bowseruk/voron-2-300/stl/Electronics Bay/Wago_3x_221-415_DIN_Mount.stl

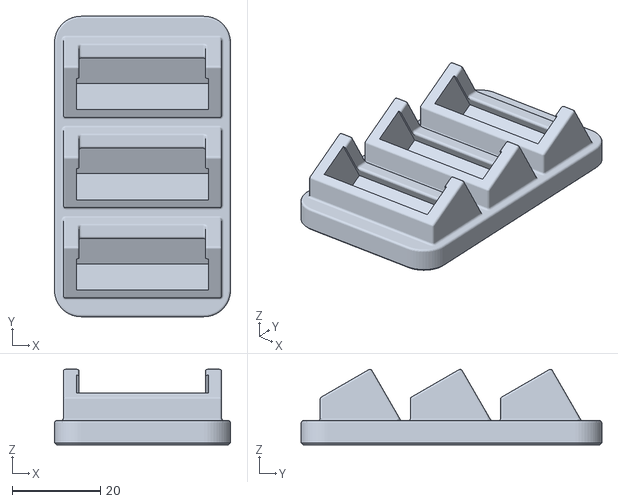
[picture p15: CAD file, 2023-08-16]
stl/Electronics Bay/Wago_3x_221-415_DIN_Mount.stl
40.0 x 68.3 x 17.2
