bowseruk/voron-2-300/stl/Exhaust FIlter/exhaust_filter_housing(r2)Filament-Sensor.stl

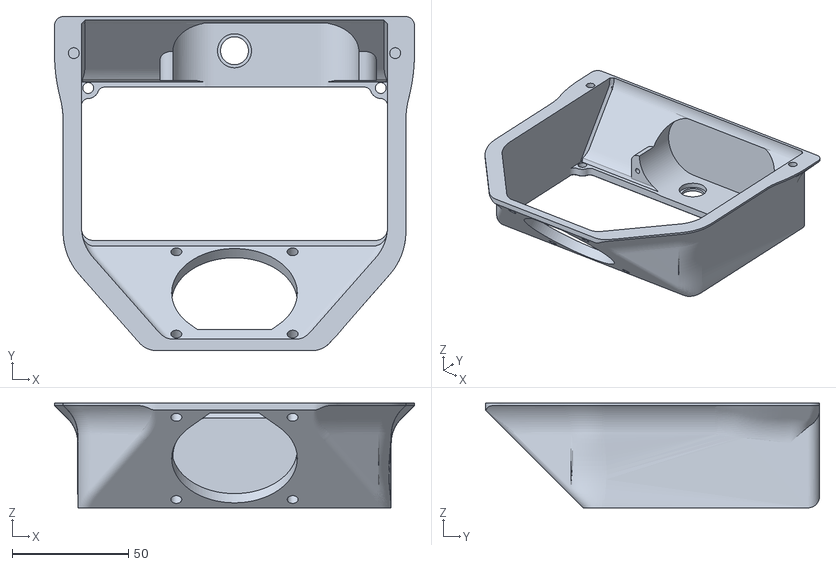
[picture p16: CAD file, 2024-02-13]
stl/Exhaust FIlter/exhaust_filter_housing(r2)Filament-Sensor.stl
154.8 x 143.7 x 45.0
