bowseruk/voron-2-300/stl/Gantry/z_joint_igus_kglm-05_x4.stl

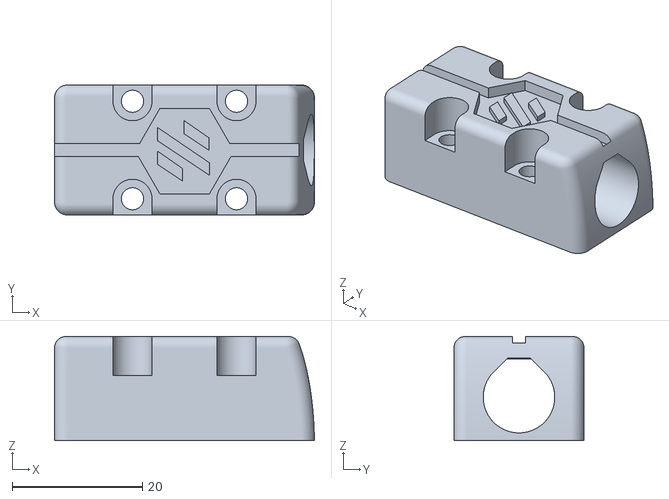
[picture p17: CAD file, 2023-08-16]
stl/Gantry/z_joint_igus_kglm-05_x4.stl
40.0 x 20.0 x 16.0
