bowseruk/voron-2-300/stl/Panel Mount/magnetic_door_hinge_tape_v2__5mm.stl

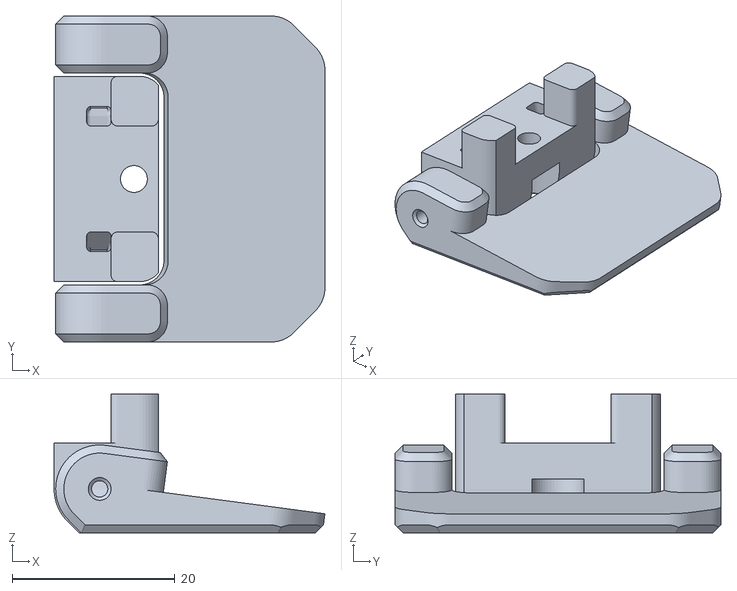
[picture p18: CAD file, 2023-12-29]
stl/Panel Mount/magnetic_door_hinge_tape_v2__5mm.stl
33.2 x 40.0 x 17.0
