bowseruk/voron-2-300/stl/Skirts/[a]_belt_guard_b_x2.stl

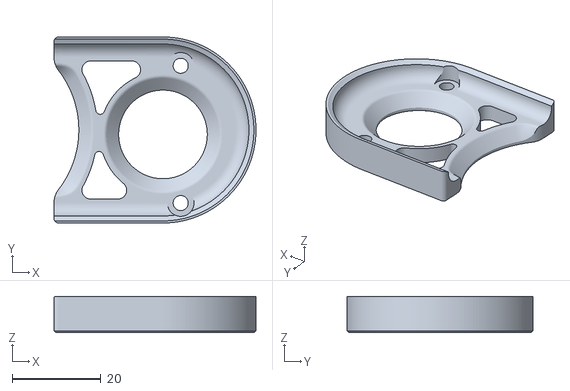
[picture p19: CAD file, 2023-08-16]
stl/Skirts/[a]_belt_guard_b_x2.stl
45.6 x 42.0 x 8.20
