bowseruk/voron-2-300/stl/Spool Management/bowden_retainer.stl

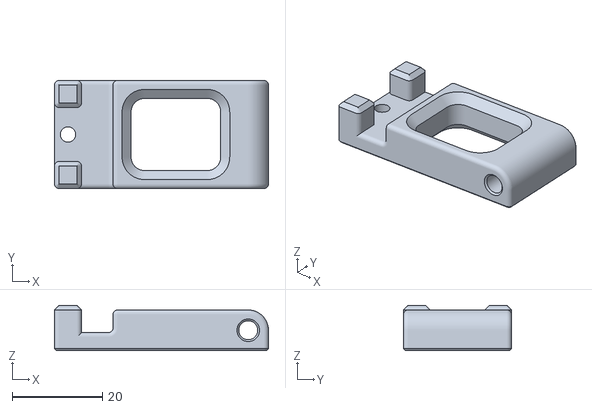
[picture p20: CAD file, 2023-08-16]
stl/Spool Management/bowden_retainer.stl
47.5 x 24.0 x 10.00
