bowseruk/voron-2-300/stl/Stealthburner/cable_door_for_pcb.stl

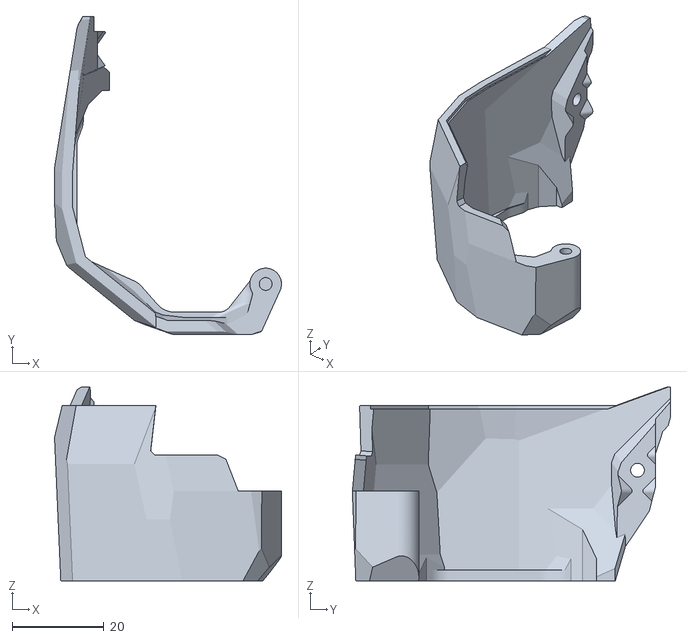
[picture p21: CAD file, 2023-08-16]
stl/Stealthburner/cable_door_for_pcb.stl
49.5 x 69.4 x 42.2
