bowseruk/voron-2-300/stl/Tools/MGN9_rail_guide_x2.stl

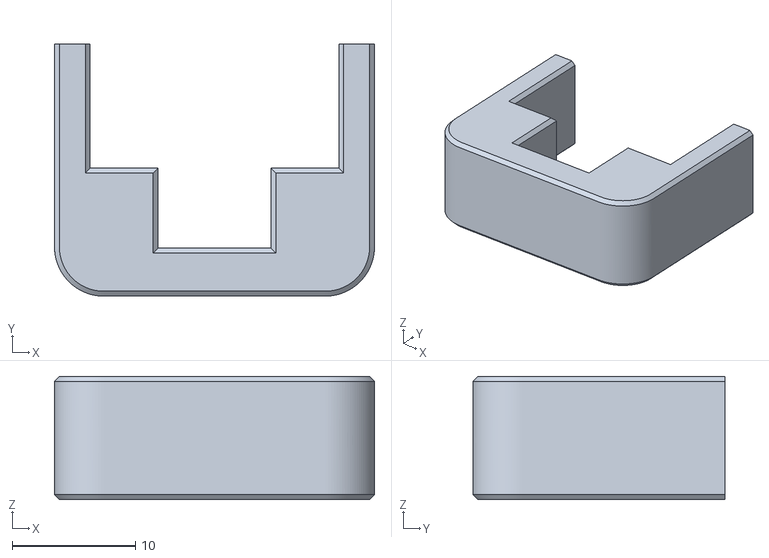
[picture p22: CAD file, 2023-08-16]
stl/Tools/MGN9_rail_guide_x2.stl
26.0 x 20.5 x 10.0
