bowseruk/voron-2-300/stl/Bed/Bed_WAGO.stl

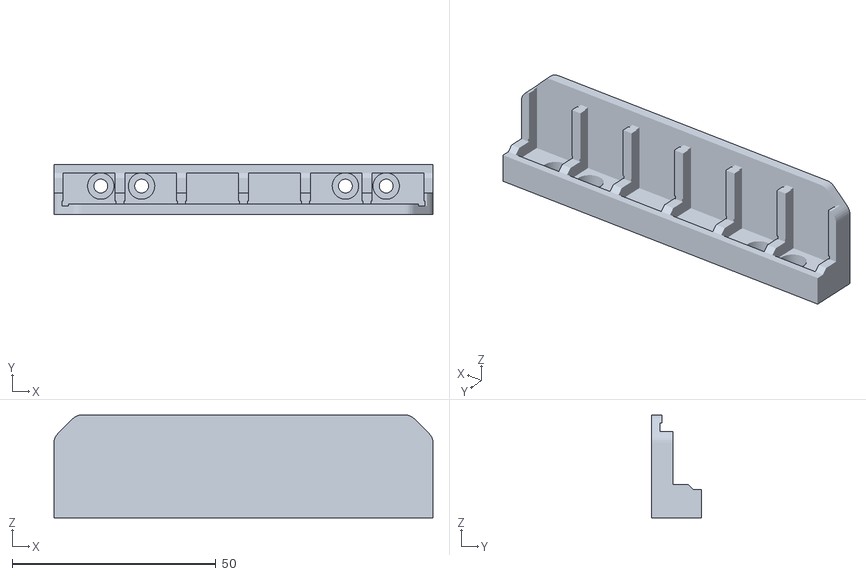
[picture p23: CAD file, 2023-08-16]
stl/Bed/Bed_WAGO.stl
92.9 x 12.2 x 25.3
