bowseruk/voron-2-300/stl/Electronics Bay/BTT_UPS_24V_DIN.stl

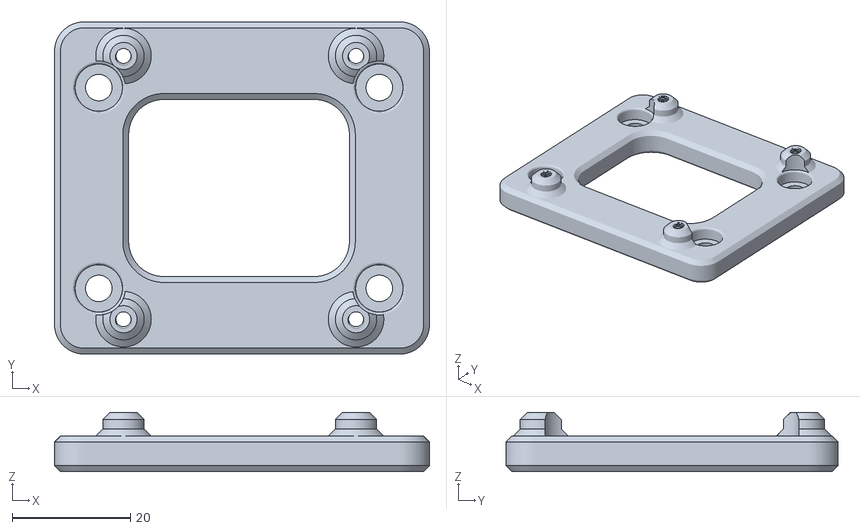
[picture p24: CAD file, 2023-08-16]
stl/Electronics Bay/BTT_UPS_24V_DIN.stl
63.5 x 56.2 x 10.0
