bowseruk/voron-2-300/stl/Exhaust FIlter/1_coal_with_mesh.stl

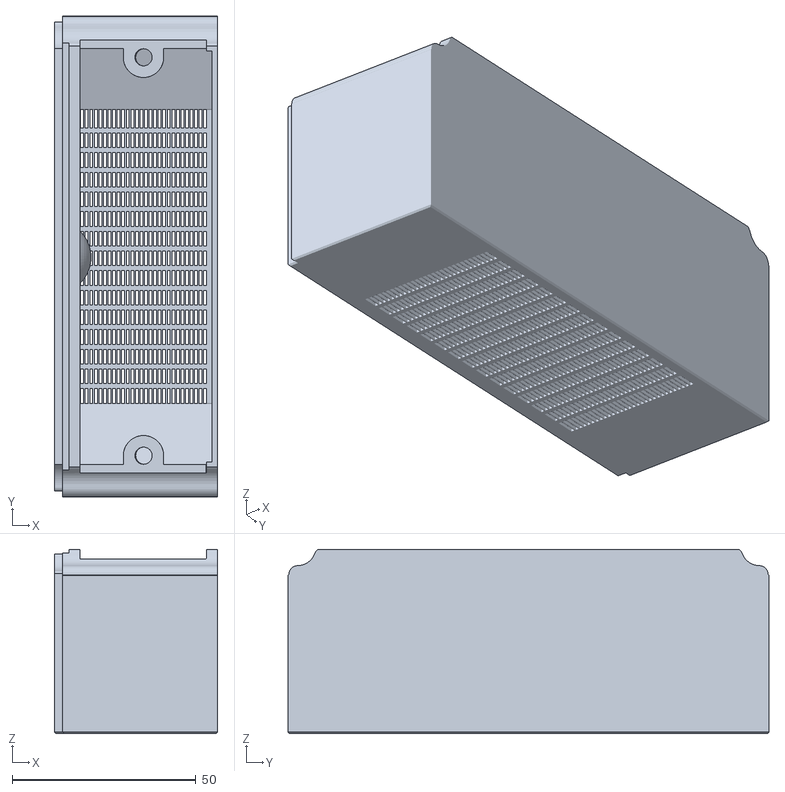
[picture p25: CAD file, 2024-02-13]
stl/Exhaust FIlter/1_coal_with_mesh.stl
44.5 x 131.0 x 50.2
