bowseruk/voron-2-300/stl/Frame/Short_Arm.stl

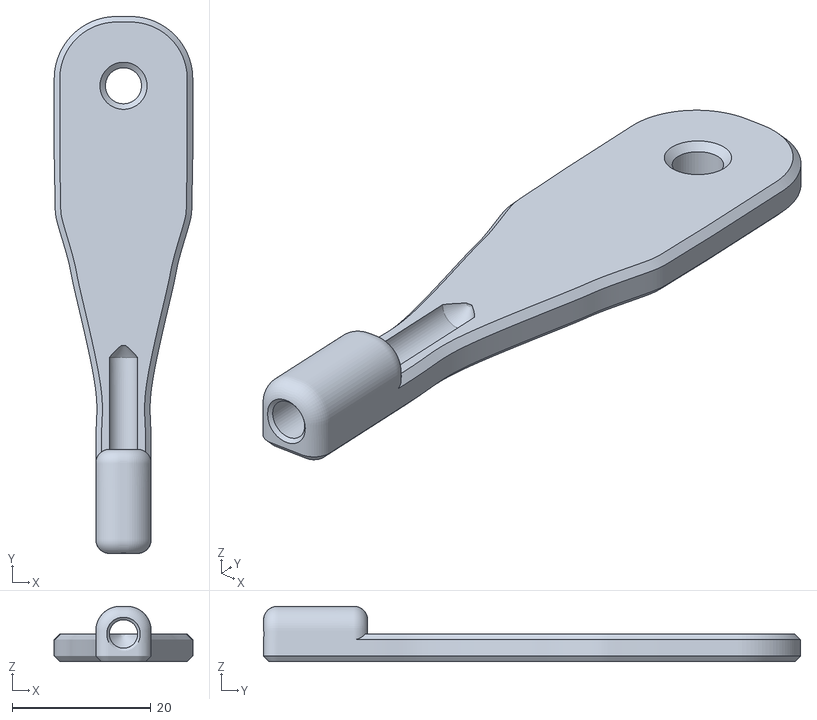
[picture p26: CAD file, 2023-08-30]
stl/Frame/Short_Arm.stl
20.0 x 77.5 x 8.00
