bowseruk/voron-2-300/stl/Gantry/z_joint_ge5c_igus_eglm-05_hall_effect_x1.stl

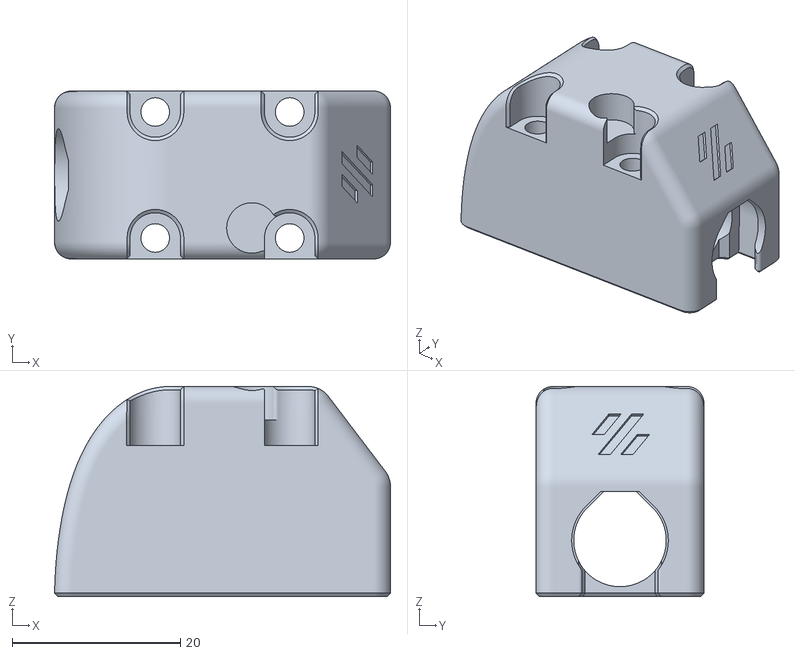
[picture p27: CAD file, 2023-08-16]
stl/Gantry/z_joint_ge5c_igus_eglm-05_hall_effect_x1.stl
40.0 x 20.0 x 25.0
