bowseruk/voron-2-300/stl/Panel Mount/Corner-Clip-7mm.stl

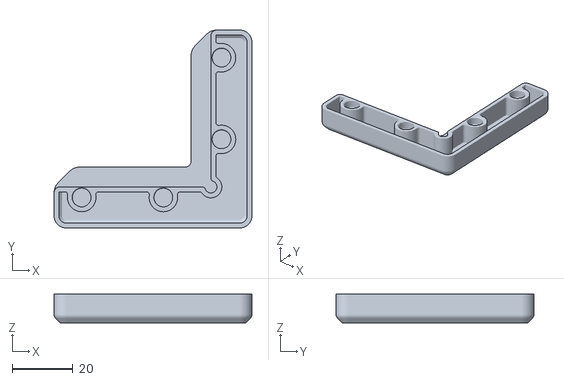
[picture p28: CAD file, 2023-12-29]
stl/Panel Mount/Corner-Clip-7mm.stl
65.0 x 65.0 x 9.50
