bowseruk/voron-2-300/stl/Skirts/front_skirt_b_300.stl

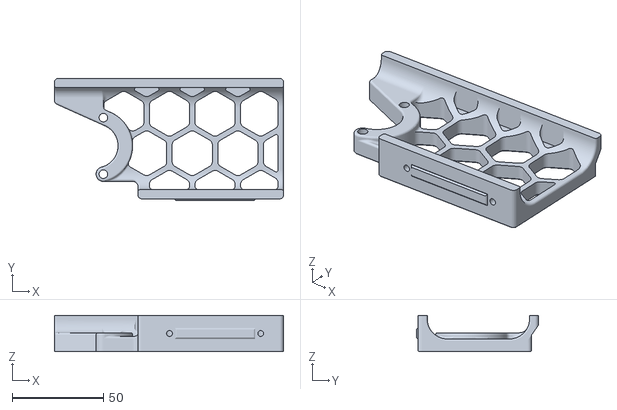
[picture p29: CAD file, 2023-08-16]
stl/Skirts/front_skirt_b_300.stl
125.5 x 67.0 x 20.0
