bowseruk/voron-2-300/stl/Stealthburner/stealthburner_printhead_dragon_rear_cw2.stl

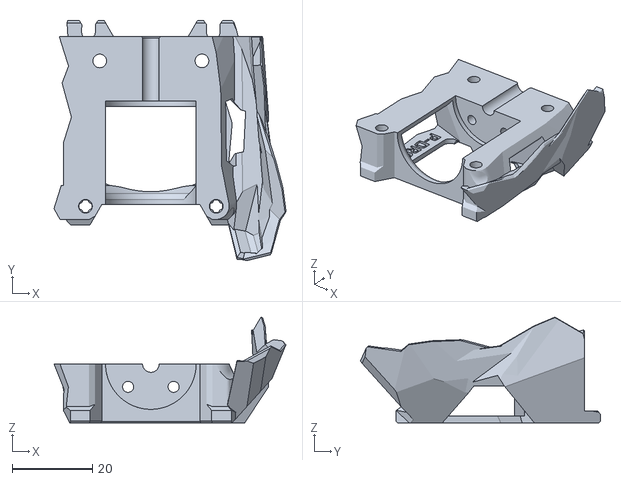
[picture p30: CAD file, 2023-08-16]
stl/Stealthburner/stealthburner_printhead_dragon_rear_cw2.stl
57.7 x 59.7 x 26.3
