bowseruk/voron-2-300/stl/Tools/pulley_jig.stl

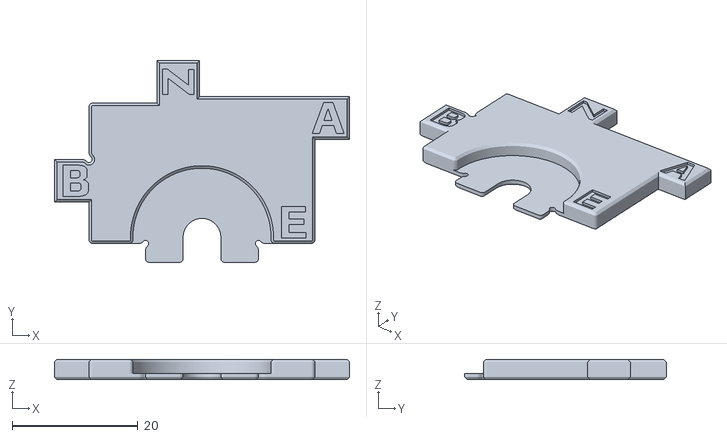
[picture p31: CAD file, 2023-08-16]
stl/Tools/pulley_jig.stl
47.0 x 32.2 x 3.20
