bowseruk/voron-2-300/stl/Z Drive/[a]_z_drive_baseplate_a_x2.stl

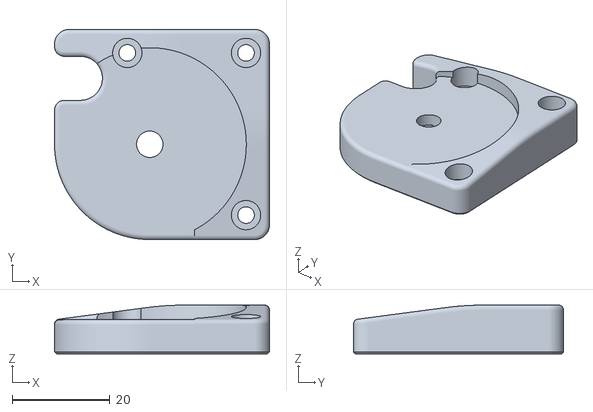
[picture p32: CAD file, 2023-08-16]
stl/Z Drive/[a]_z_drive_baseplate_a_x2.stl
44.0 x 43.0 x 10.0
