bowseruk/voron-2-300/stl/Bed/V2_Duo_Plenum.stl

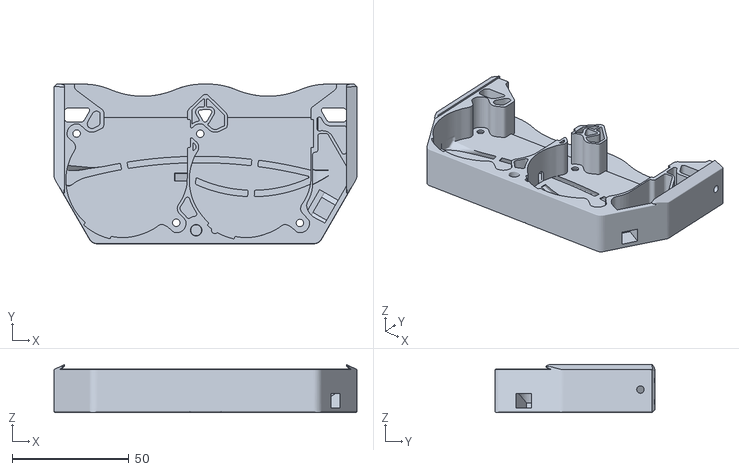
[picture p33: CAD file, 2023-08-16]
stl/Bed/V2_Duo_Plenum.stl
130.0 x 68.6 x 20.6
