bowseruk/voron-2-300/stl/Electronics Bay/RPI_Metal_DIN_Mount.stl

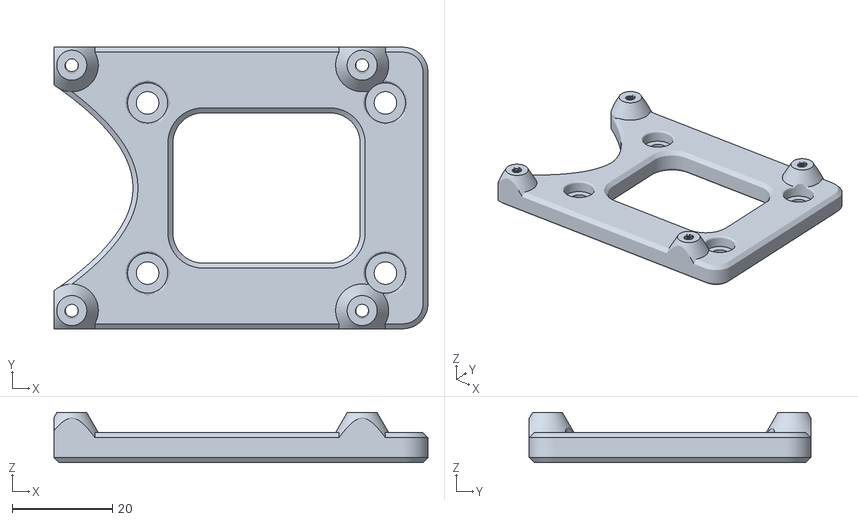
[picture p34: CAD file, 2023-08-16]
stl/Electronics Bay/RPI_Metal_DIN_Mount.stl
74.7 x 56.2 x 10.0
