bowseruk/voron-2-300/stl/Exhaust FIlter/1_hepa.stl

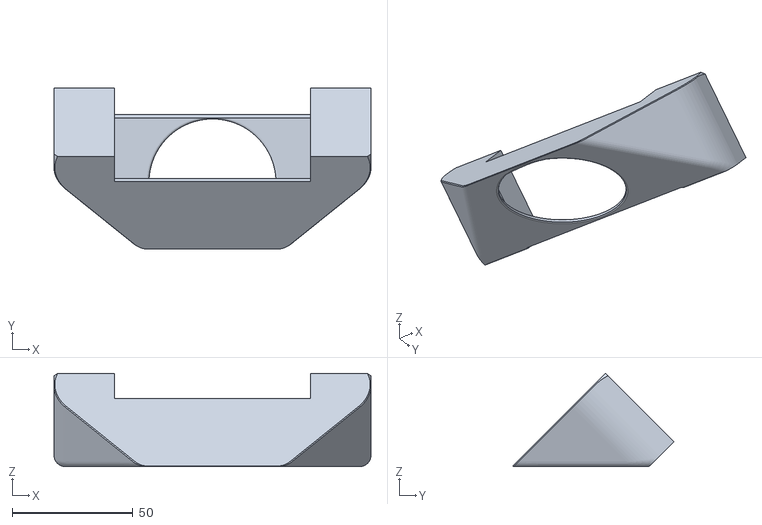
[picture p35: CAD file, 2024-02-13]
stl/Exhaust FIlter/1_hepa.stl
131.1 x 66.6 x 38.5
