bowseruk/voron-2-300/stl/Frame/arm_mount_over_led.stl

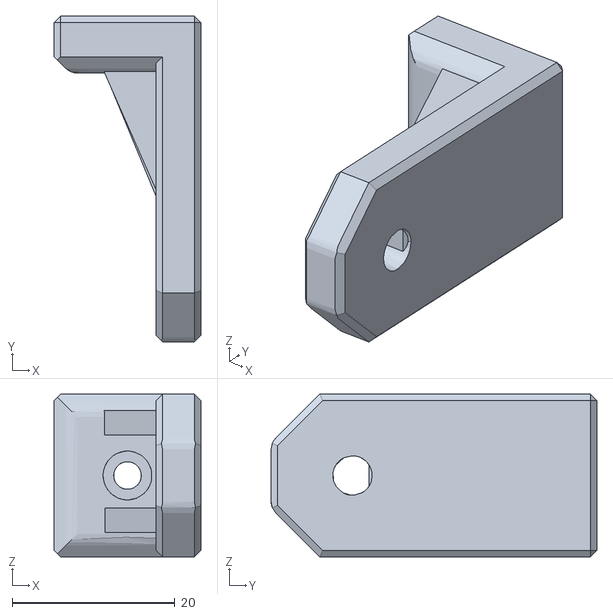
[picture p36: CAD file, 2023-08-30]
stl/Frame/arm_mount_over_led.stl
18.0 x 40.0 x 20.0
