bowseruk/voron-2-300/stl/Gantry/Z_Chain_Guide_Thermistor_Mount.stl

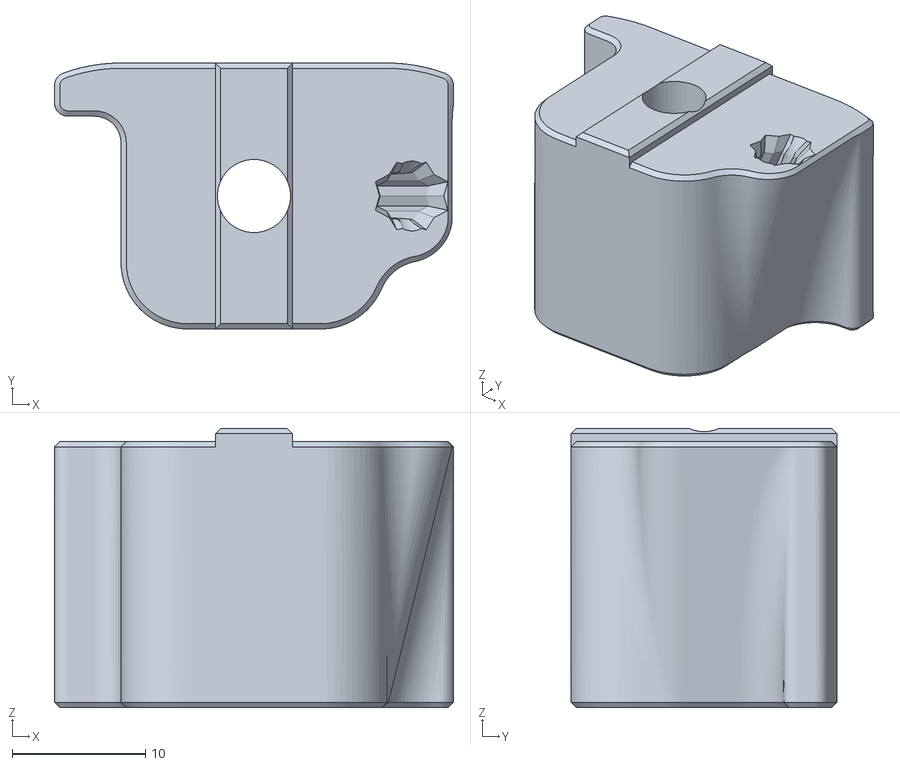
[picture p37: CAD file, 2023-08-16]
stl/Gantry/Z_Chain_Guide_Thermistor_Mount.stl
30.0 x 20.0 x 21.0
