bowseruk/voron-2-300/stl/Panel Mount/Corner-Clip-6mm.stl

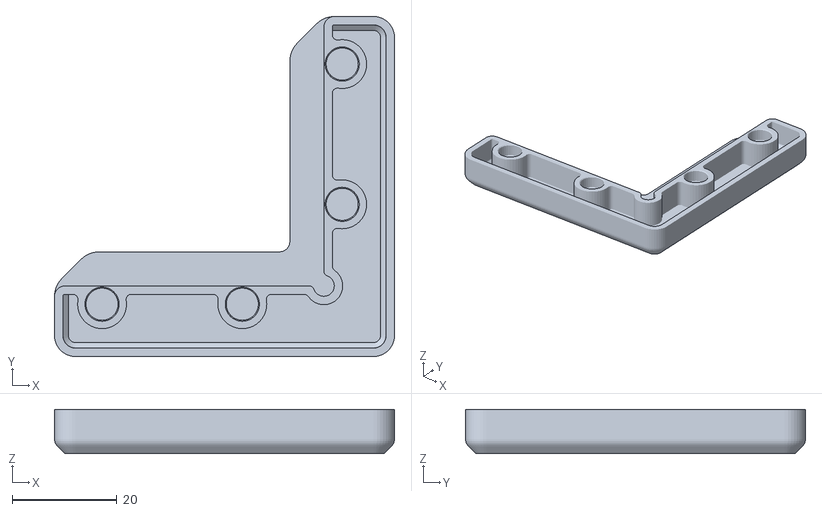
[picture p38: CAD file, 2023-12-29]
stl/Panel Mount/Corner-Clip-6mm.stl
65.0 x 65.0 x 8.50
