bowseruk/voron-2-300/stl/Skirts/[a]_keystone_blank_insert.stl

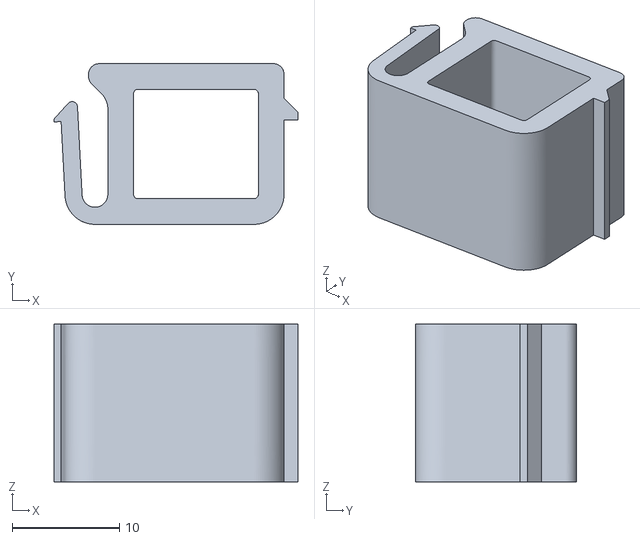
[picture p39: CAD file, 2023-08-16]
stl/Skirts/[a]_keystone_blank_insert.stl
22.8 x 15.0 x 14.7
