bowseruk/voron-2-300/stl/Stealthburner/[o]_stealthburner_LED_carrier.stl

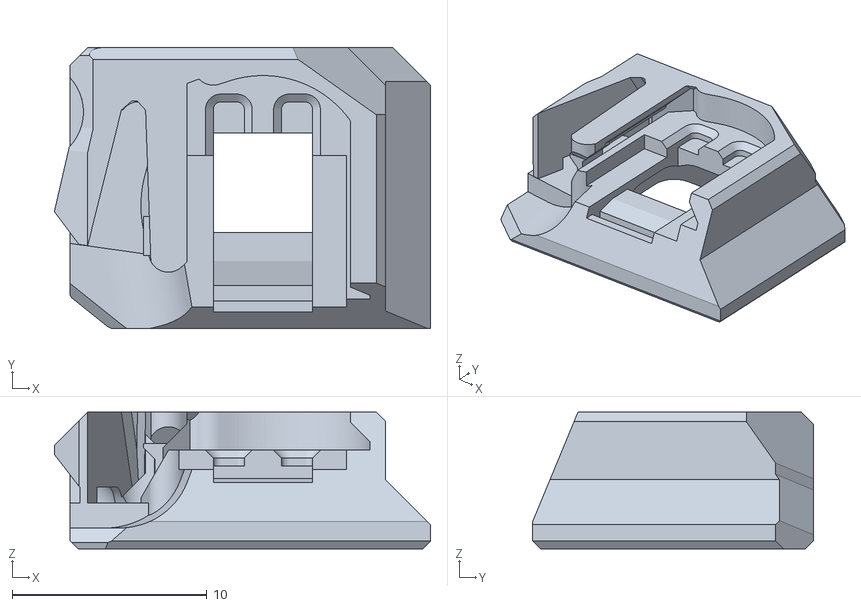
[picture p40: CAD file, 2023-08-16]
stl/Stealthburner/[o]_stealthburner_LED_carrier.stl
19.3 x 14.4 x 7.01
