bowseruk/voron-2-300/stl/Tools/MGN12_rail_guide_x2.stl

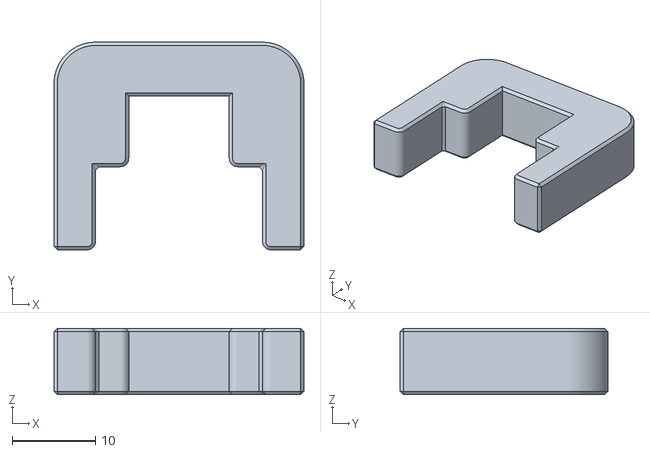
[picture p41: CAD file, 2023-08-16]
stl/Tools/MGN12_rail_guide_x2.stl
30.1 x 25.0 x 8.00
