bowseruk/voron-2-300/stl/Z Drive/z_motor_mount_b_x2.stl

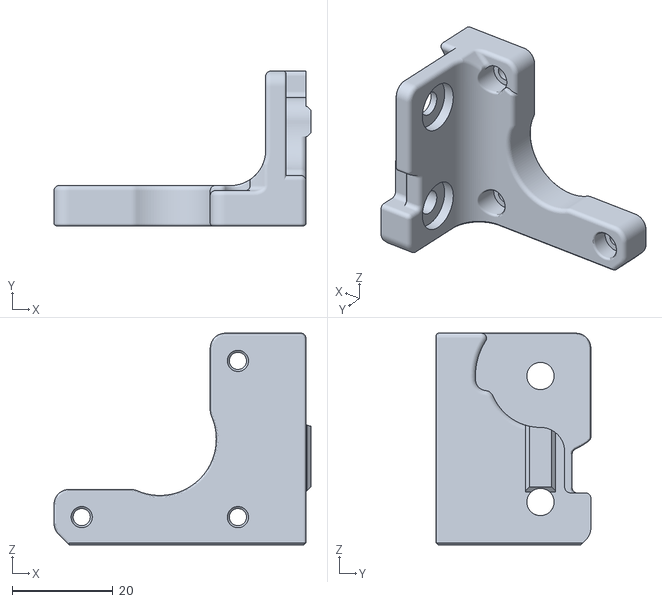
[picture p42: CAD file, 2023-08-16]
stl/Z Drive/z_motor_mount_b_x2.stl
51.0 x 30.7 x 42.0
