bowseruk/voron-2-300/stl/Bed/V2_Duo_Plenum_LID.stl

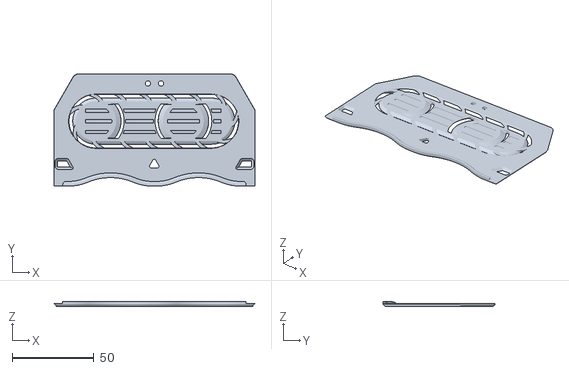
[picture p43: CAD file, 2023-08-16]
stl/Bed/V2_Duo_Plenum_LID.stl
122.8 x 68.5 x 2.80
