bowseruk/voron-2-300/stl/Electronics Bay/wago_221-415_mount_3by5.stl

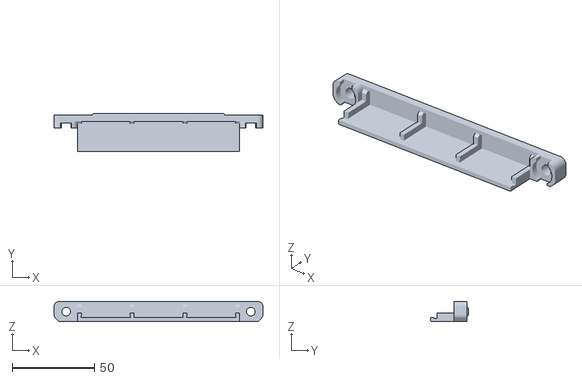
[picture p44: CAD file, 2023-08-16]
stl/Electronics Bay/wago_221-415_mount_3by5.stl
126.8 x 23.0 x 12.2
