bowseruk/voron-2-300/stl/Exhaust FIlter/exhaust_filter_housing.stl

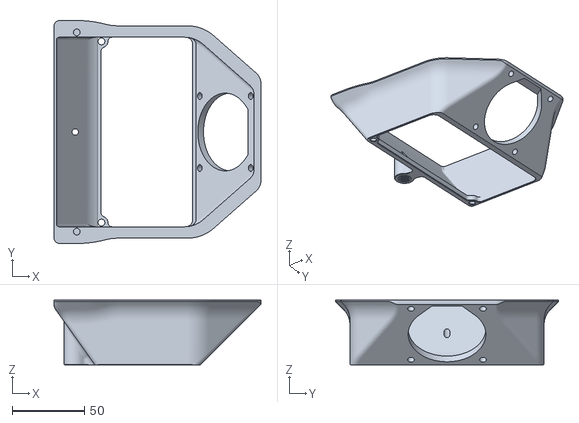
[picture p45: CAD file, 2023-08-16]
stl/Exhaust FIlter/exhaust_filter_housing.stl
143.7 x 154.8 x 45.0
