bowseruk/voron-2-300/stl/Frame/[a]_handle_middle_part.stl

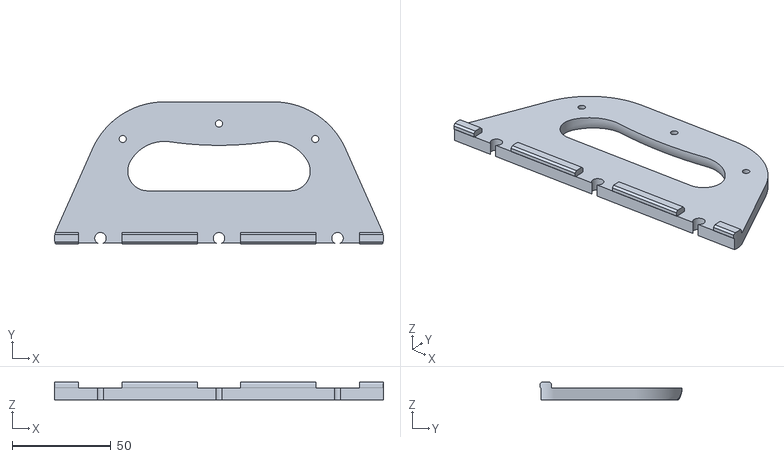
[picture p46: CAD file, 2023-08-21]
stl/Frame/[a]_handle_middle_part.stl
166.5 x 72.0 x 9.00
