bowseruk/voron-2-300/stl/Gantry/[a]_z_belt_clip_upper_x4.stl

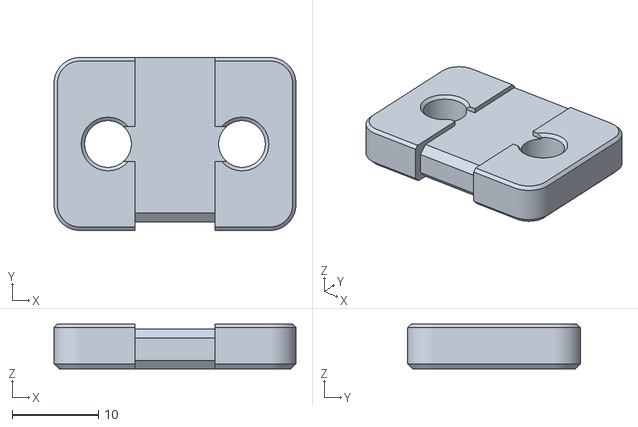
[picture p47: CAD file, 2023-08-16]
stl/Gantry/[a]_z_belt_clip_upper_x4.stl
28.0 x 20.0 x 5.20
