bowseruk/voron-2-300/stl/Panel Mount/Midspan-Clip-4mm.stl

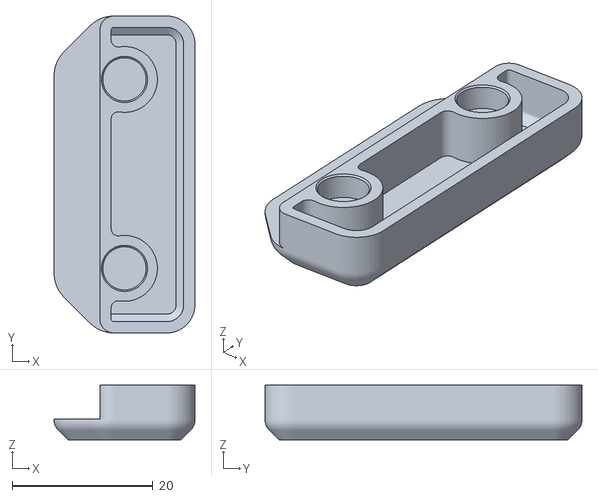
[picture p48: CAD file, 2023-12-29]
stl/Panel Mount/Midspan-Clip-4mm.stl
20.0 x 45.0 x 7.80
