bowseruk/voron-2-300/stl/Skirts/side_fan_support_x2.stl

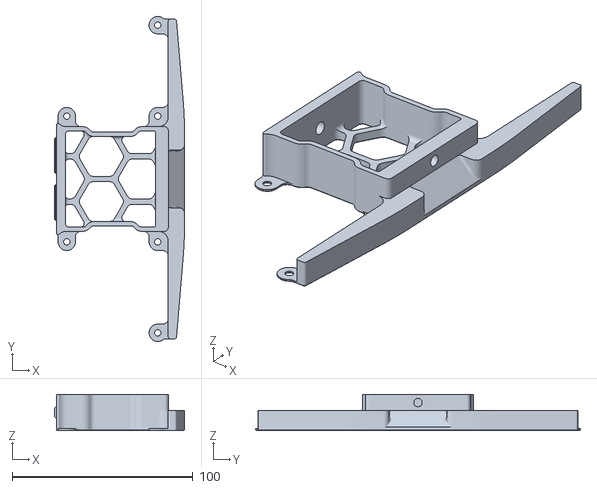
[picture p49: CAD file, 2023-08-16]
stl/Skirts/side_fan_support_x2.stl
72.0 x 180.0 x 20.0
