bowseruk/voron-2-300/stl/Stealthburner/[c]_stealthburner_LED_diffuser.stl

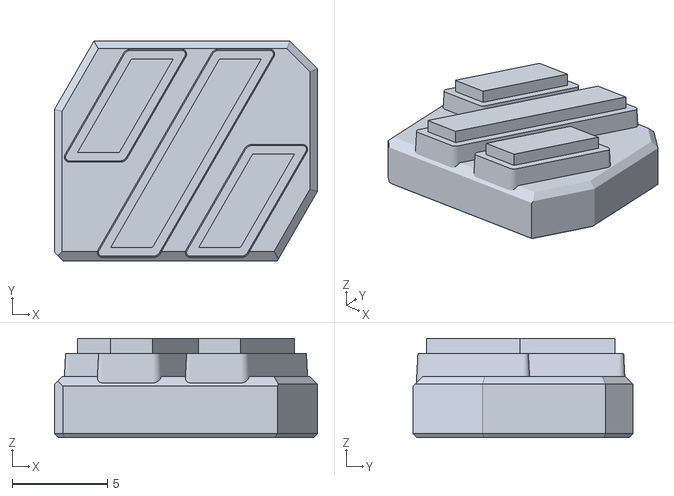
[picture p50: CAD file, 2023-08-16]
stl/Stealthburner/[c]_stealthburner_LED_diffuser.stl
13.8 x 11.5 x 5.20
