bowseruk/voron-2-300/stl/Tools/[a]_guidler_b.stl

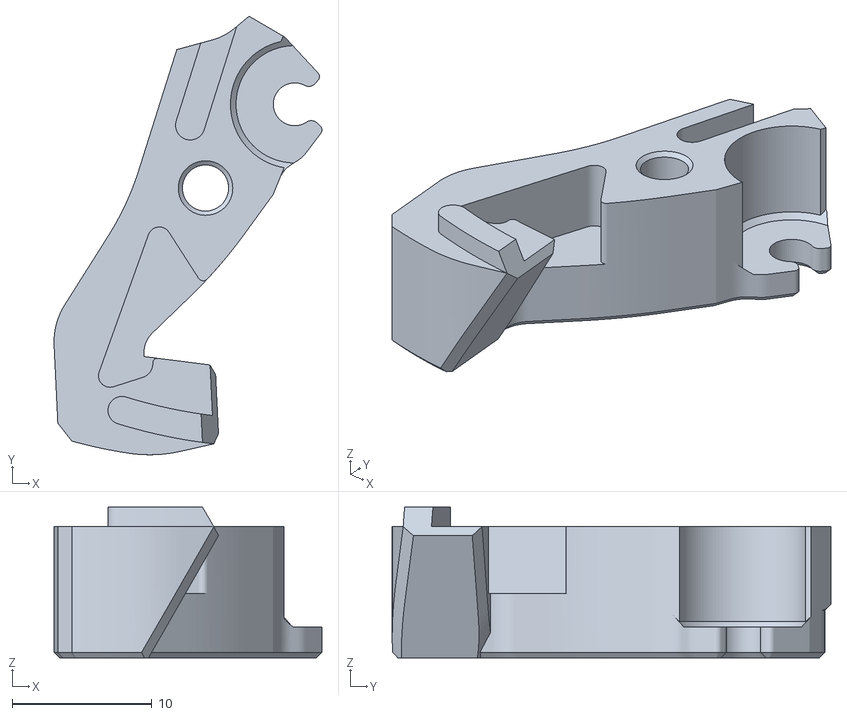
[picture p51: CAD file, 2023-08-16]
stl/Tools/[a]_guidler_b.stl
19.2 x 31.4 x 10.8
