bowseruk/voron-2-300/stl/Electronics Bay/pcb_din_clip_x3.stl

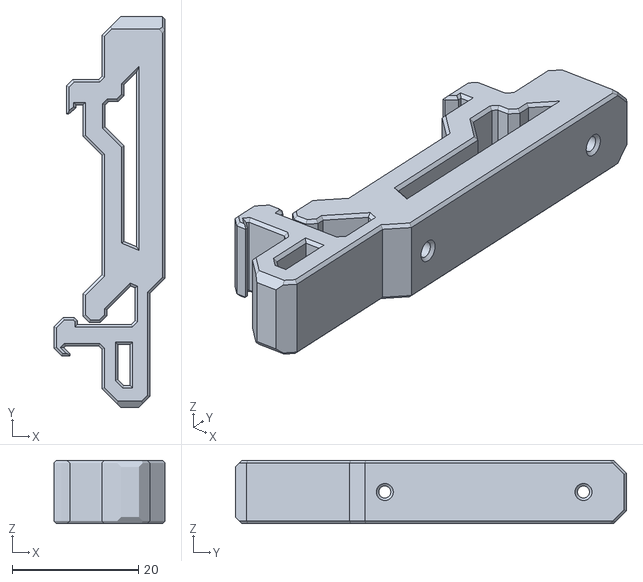
[picture p52: CAD file, 2023-08-16]
stl/Electronics Bay/pcb_din_clip_x3.stl
17.6 x 62.0 x 10.0
