bowseruk/voron-2-300/stl/Exhaust FIlter/exhaust_filter_grill.stl

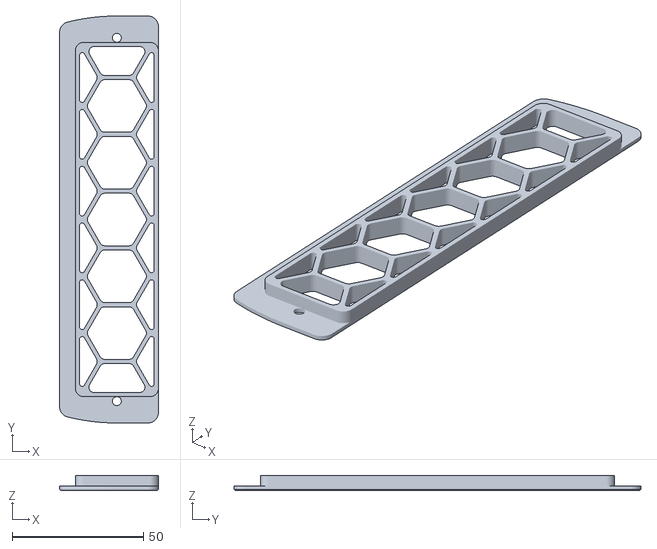
[picture p53: CAD file, 2023-08-16]
stl/Exhaust FIlter/exhaust_filter_grill.stl
37.6 x 154.8 x 5.60
