bowseruk/voron-2-300/stl/Frame/LED Spacer.stl

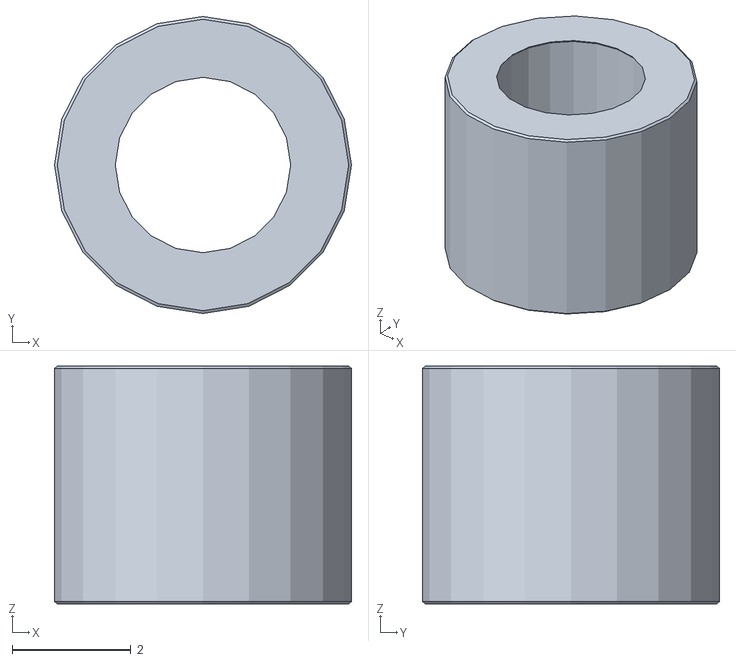
[picture p54: CAD file, 2023-08-20]
stl/Frame/LED Spacer.stl
5.00 x 5.00 x 4.00
