bowseruk/voron-2-300/stl/Gantry/[a]_z_chain_retainer_bracket_x2.stl

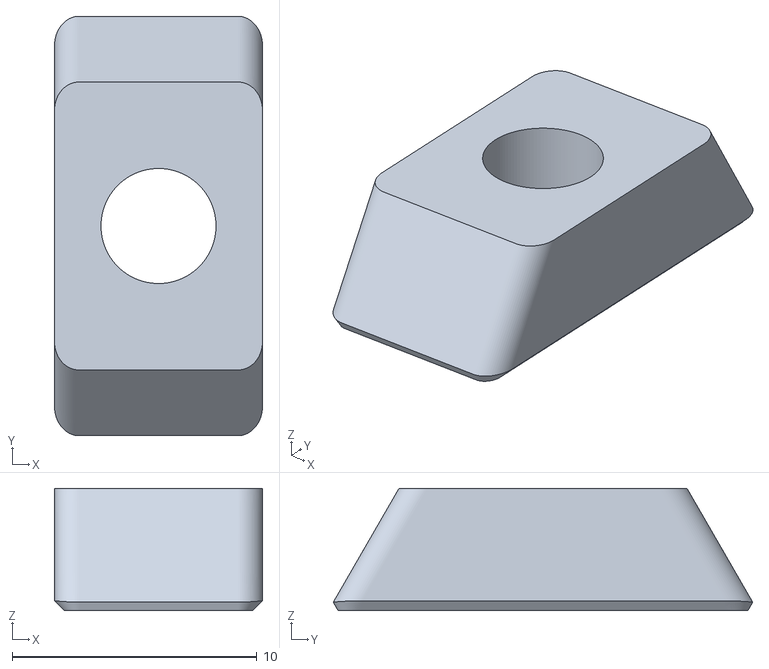
[picture p55: CAD file, 2023-08-16]
stl/Gantry/[a]_z_chain_retainer_bracket_x2.stl
8.50 x 17.1 x 5.00
