bowseruk/voron-2-300/stl/Panel Mount/Midspan-Clip-6mm.stl

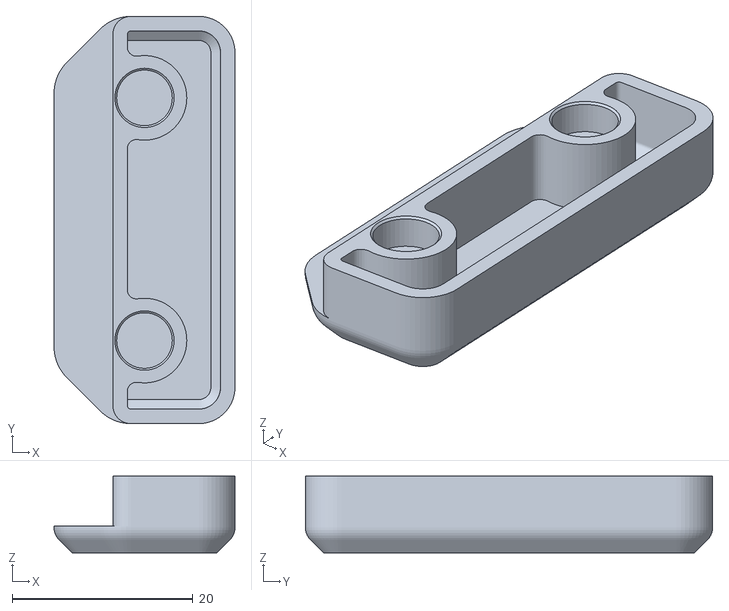
[picture p56: CAD file, 2023-12-29]
stl/Panel Mount/Midspan-Clip-6mm.stl
20.0 x 45.0 x 8.50
