bowseruk/voron-2-300/stl/Skirts/[a]_mini12864_case_hinge.stl

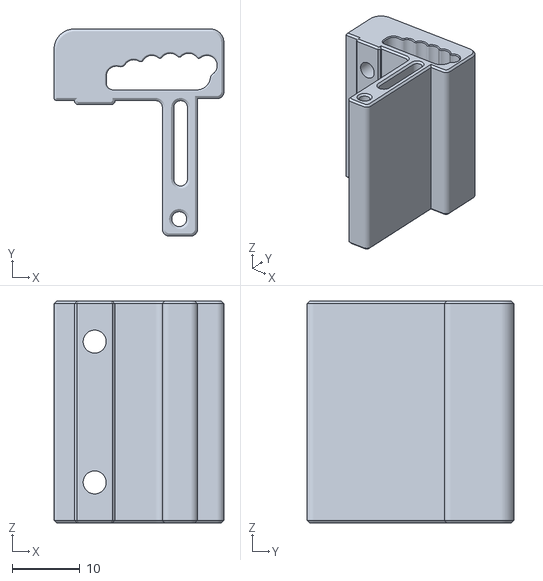
[picture p57: CAD file, 2023-08-16]
stl/Skirts/[a]_mini12864_case_hinge.stl
25.1 x 30.6 x 32.8
