bowseruk/voron-2-300/stl/Stealthburner/[o]_stealthburner_LED_diffuser_mask.stl

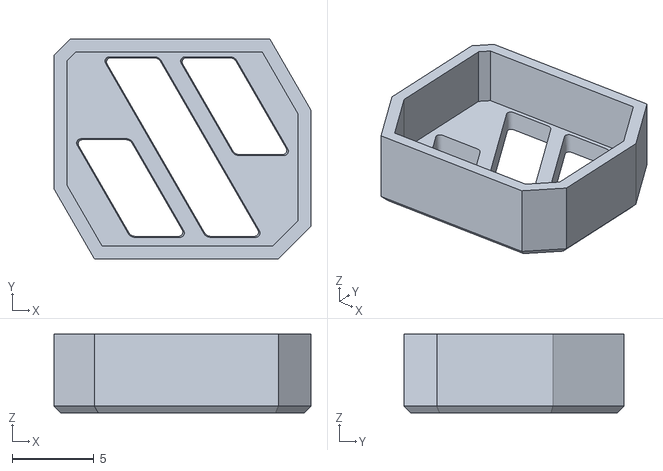
[picture p58: CAD file, 2023-08-16]
stl/Stealthburner/[o]_stealthburner_LED_diffuser_mask.stl
15.7 x 13.4 x 4.80
