bowseruk/voron-2-300/stl/Tools/bed_hole_marking_template_x1_Rev2.STL

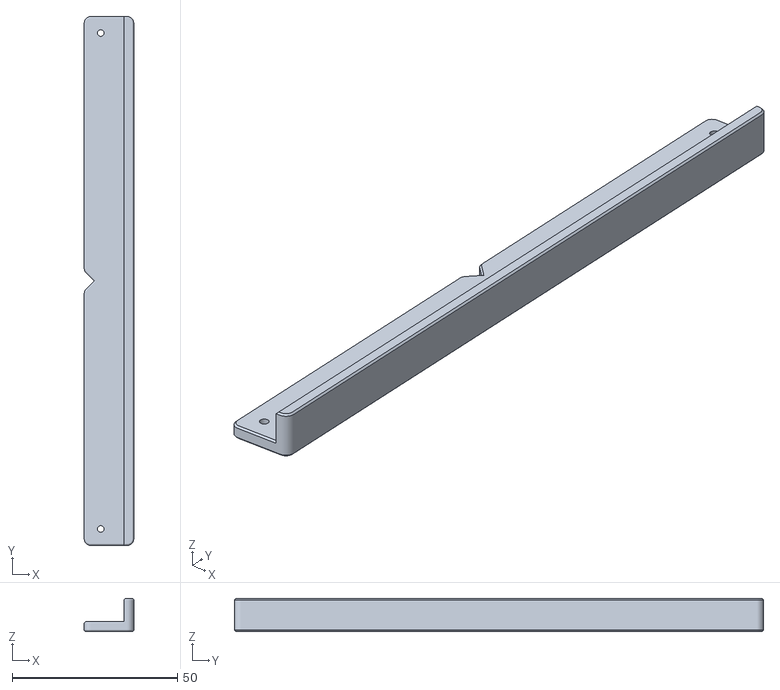
[picture p59: CAD file, 2023-08-16]
stl/Tools/bed_hole_marking_template_x1_Rev2.STL
15.0 x 160.0 x 10.0
