bowseruk/voron-2-300/stl/Z Drive/[a]_belt_tensioner_a_x2.stl

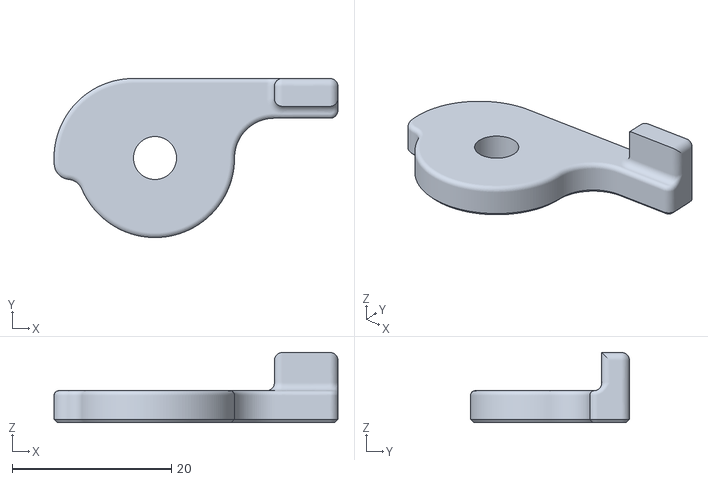
[picture p60: CAD file, 2023-08-16]
stl/Z Drive/[a]_belt_tensioner_a_x2.stl
35.7 x 20.0 x 8.80
