bowseruk/voron-2-300/stl/Bed/Bed_Support_Alignment_Tool_Center_250_300_350_x2.stl

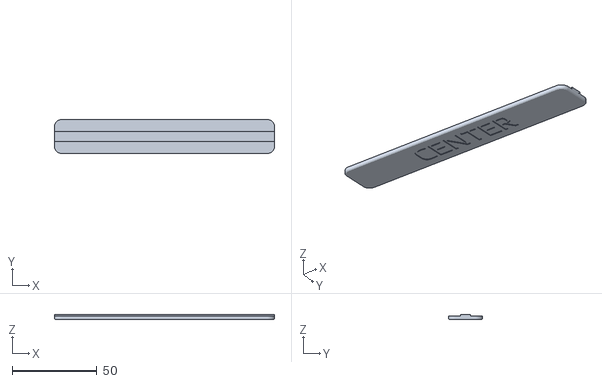
[picture p61: CAD file, 2023-08-16]
stl/Bed/Bed_Support_Alignment_Tool_Center_250_300_350_x2.stl
130.0 x 20.0 x 2.99
