bowseruk/voron-2-300/stl/Electronics Bay/PSU_stabilizer_50mm.stl

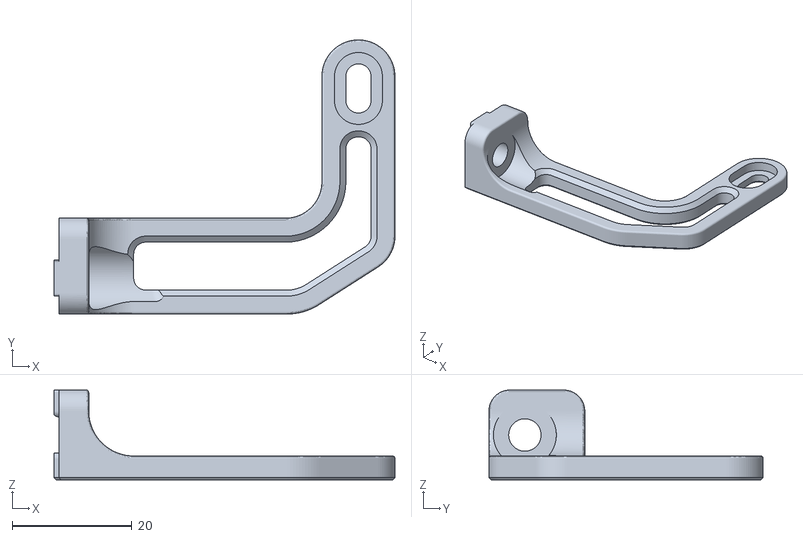
[picture p62: CAD file, 2023-08-16]
stl/Electronics Bay/PSU_stabilizer_50mm.stl
56.9 x 45.7 x 15.0
