bowseruk/voron-2-300/stl/Exhaust FIlter/[a]_exhaust_filter_mount_x2.stl

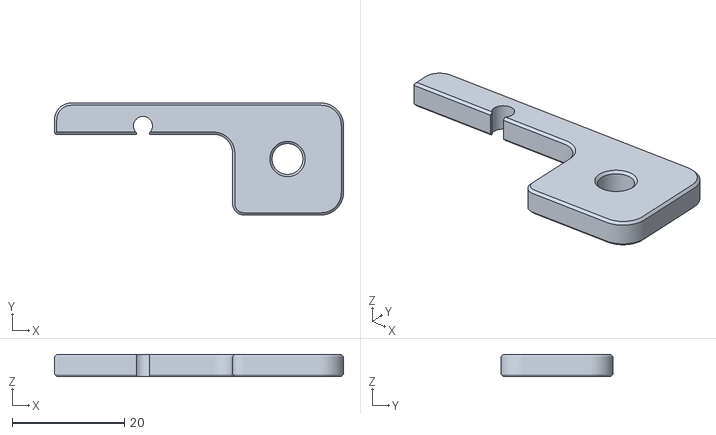
[picture p63: CAD file, 2023-08-16]
stl/Exhaust FIlter/[a]_exhaust_filter_mount_x2.stl
51.6 x 20.0 x 4.00
