bowseruk/voron-2-300/stl/Gantry/PITB Support.stl

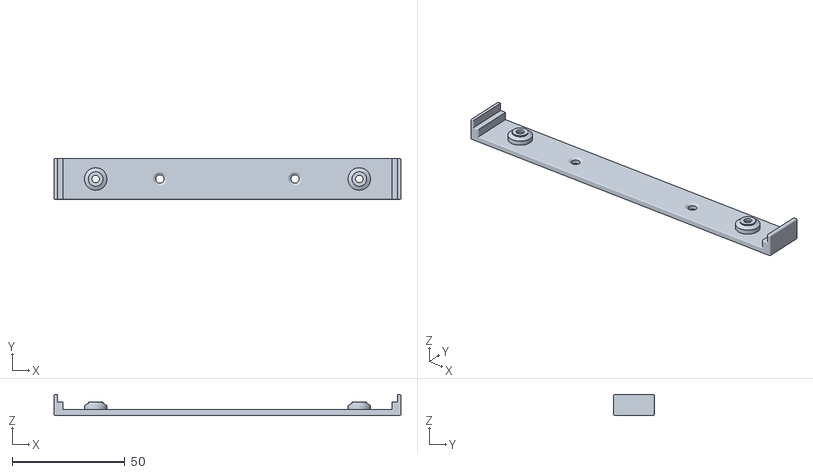
[picture p64: CAD file, 2023-08-16]
stl/Gantry/PITB Support.stl
154.0 x 18.0 x 9.40
