bowseruk/voron-2-300/stl/Panel Mount/Magnet-Insert-v2.stl

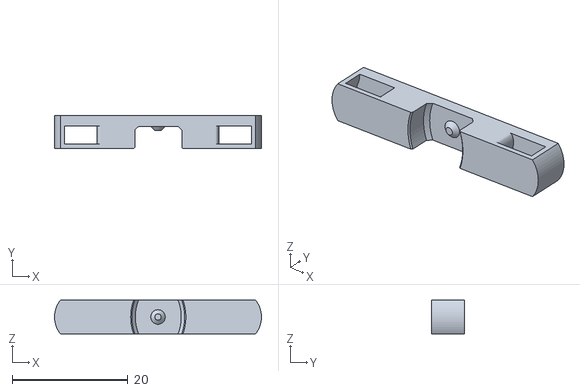
[picture p65: CAD file, 2023-12-29]
stl/Panel Mount/Magnet-Insert-v2.stl
35.7 x 5.70 x 5.80
