bowseruk/voron-2-300/stl/Skirts/[a]_fan_grill_open_optional_x2.stl

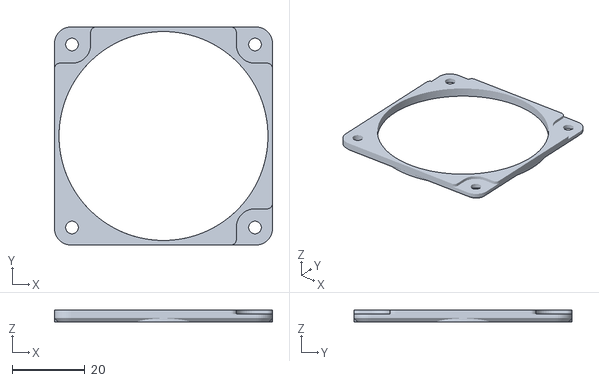
[picture p66: CAD file, 2023-08-16]
stl/Skirts/[a]_fan_grill_open_optional_x2.stl
60.0 x 60.0 x 3.20
