bowseruk/voron-2-300/stl/Stealthburner/chain_anchor_3hole.stl

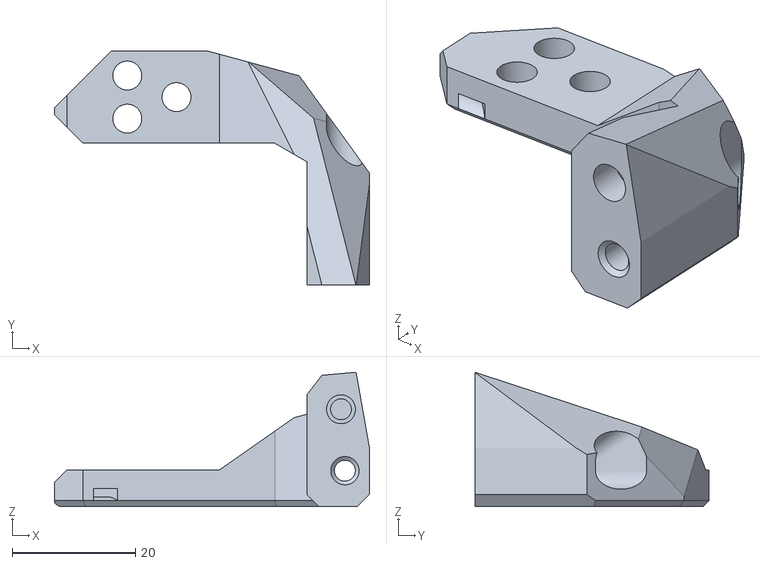
[picture p67: CAD file, 2023-08-16]
stl/Stealthburner/chain_anchor_3hole.stl
51.2 x 38.1 x 21.9
