bowseruk/voron-2-300/stl/Tools/[a]_guidler_a.stl

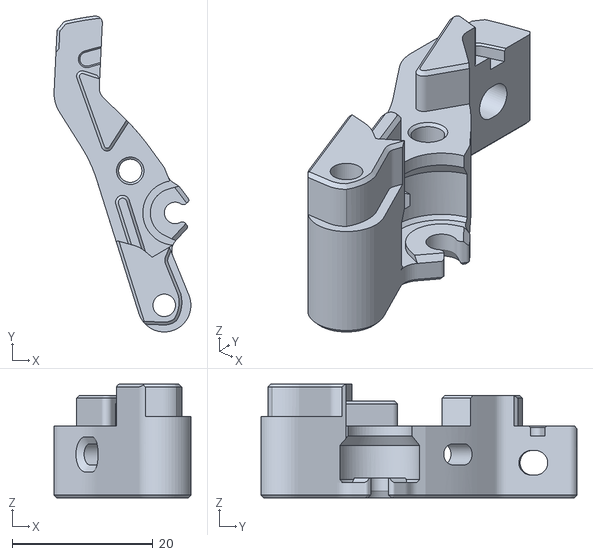
[picture p68: CAD file, 2023-08-16]
stl/Tools/[a]_guidler_a.stl
19.5 x 45.0 x 16.2
