bowseruk/voron-2-300/stl/Bed/Bed_Support_Alignment_Tool_300_Corners_x4.stl

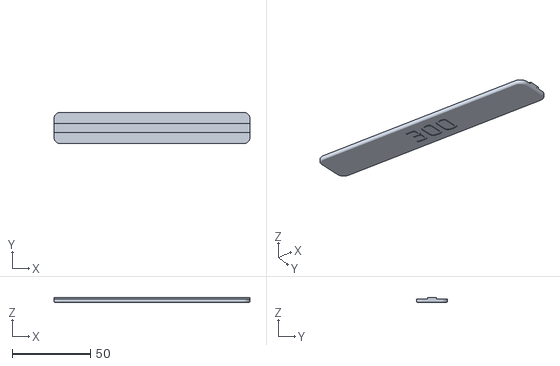
[picture p69: CAD file, 2023-08-16]
stl/Bed/Bed_Support_Alignment_Tool_300_Corners_x4.stl
125.0 x 20.0 x 2.99
