bowseruk/voron-2-300/stl/Exhaust FIlter/[a]_filter_access_cover.stl

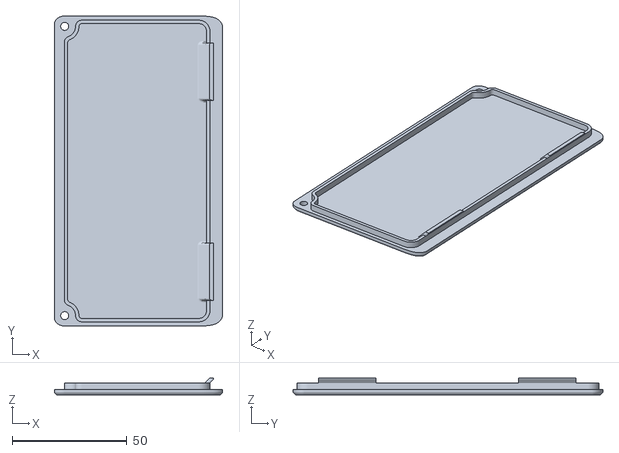
[picture p70: CAD file, 2023-08-16]
stl/Exhaust FIlter/[a]_filter_access_cover.stl
73.2 x 134.8 x 7.20
