bowseruk/voron-2-300/stl/Frame/flush_clip_small.stl

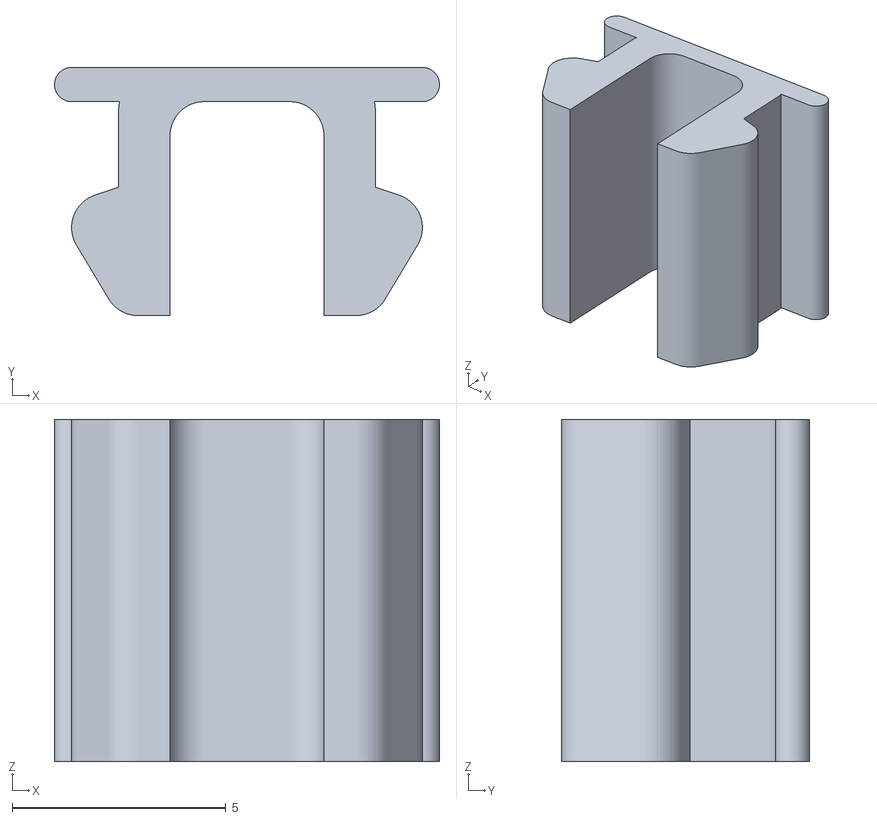
[picture p71: CAD file, 2023-08-16]
stl/Frame/flush_clip_small.stl
9.00 x 5.80 x 8.00
