bowseruk/voron-2-300/stl/Panel Mount/Install-Jig.stl

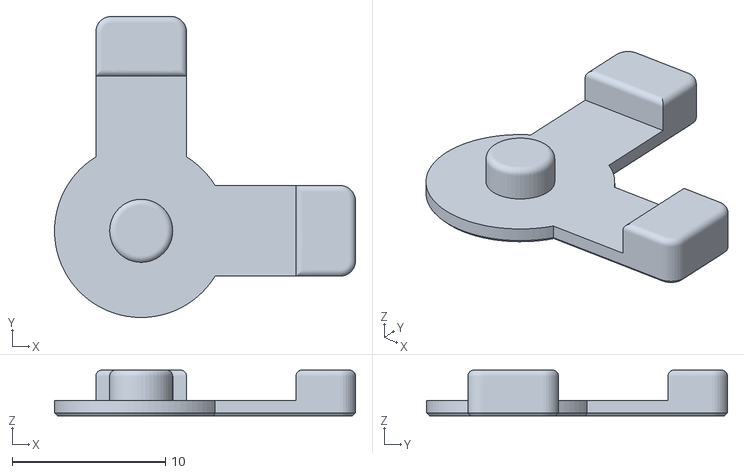
[picture p73: CAD file, 2023-12-29]
stl/Panel Mount/Install-Jig.stl
19.6 x 19.6 x 3.00
