bowseruk/voron-2-300/stl/Skirts/mini12864_case_rear.stl

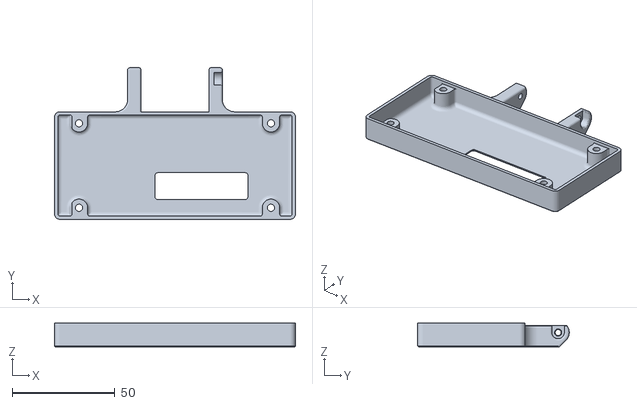
[picture p74: CAD file, 2023-08-16]
stl/Skirts/mini12864_case_rear.stl
117.0 x 73.6 x 11.6
