bowseruk/voron-2-300/stl/Tools/[a]_latch_shuttle.stl

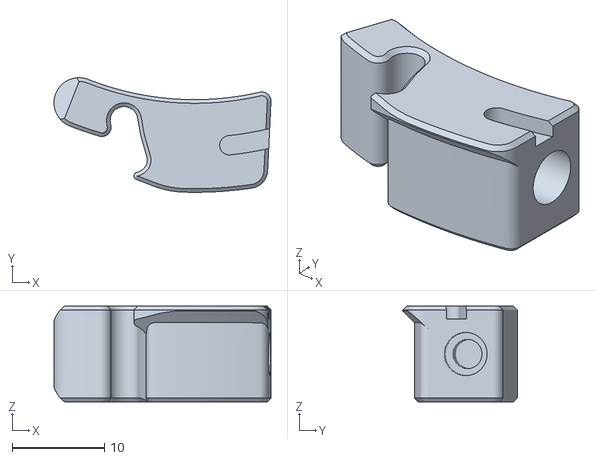
[picture p75: CAD file, 2023-08-16]
stl/Tools/[a]_latch_shuttle.stl
23.6 x 12.5 x 10.4
