bowseruk/voron-2-300/stl/Electronics Bay/Wago_3x_221-415_Skirt_Inlet_Mount.stl

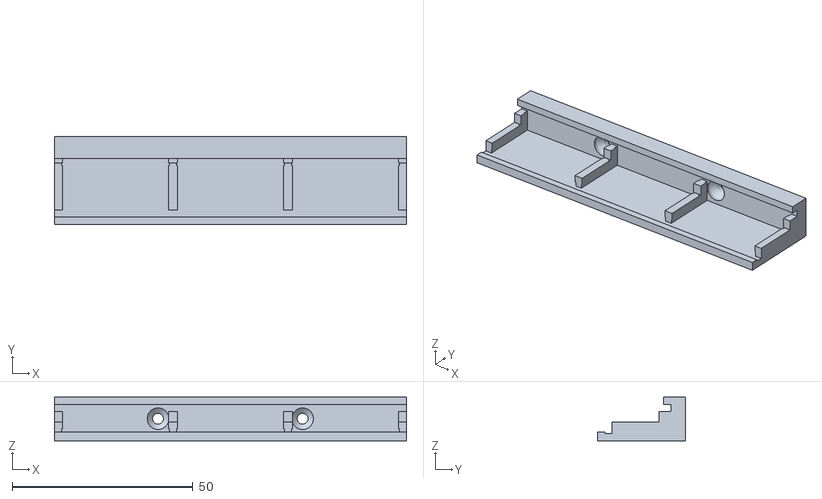
[picture p76: CAD file, 2023-08-16]
stl/Electronics Bay/Wago_3x_221-415_Skirt_Inlet_Mount.stl
97.4 x 24.2 x 12.2
