bowseruk/voron-2-300/stl/Exhaust FIlter/[a]_exhaust_fan_grill.stl

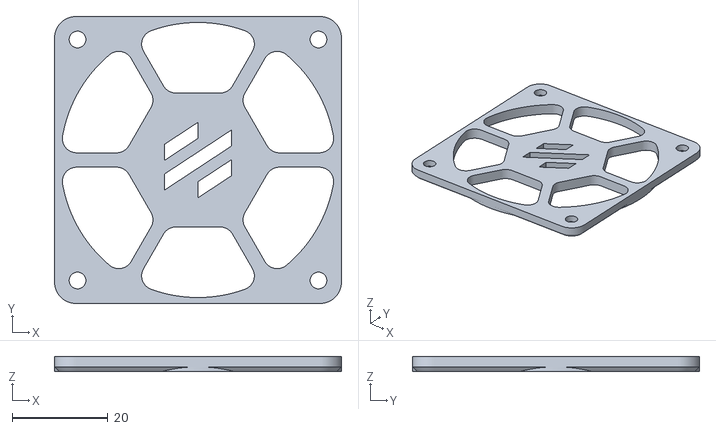
[picture p77: CAD file, 2023-08-16]
stl/Exhaust FIlter/[a]_exhaust_fan_grill.stl
60.0 x 60.0 x 3.20
