bowseruk/voron-2-300/stl/Frame/clip_small.stl

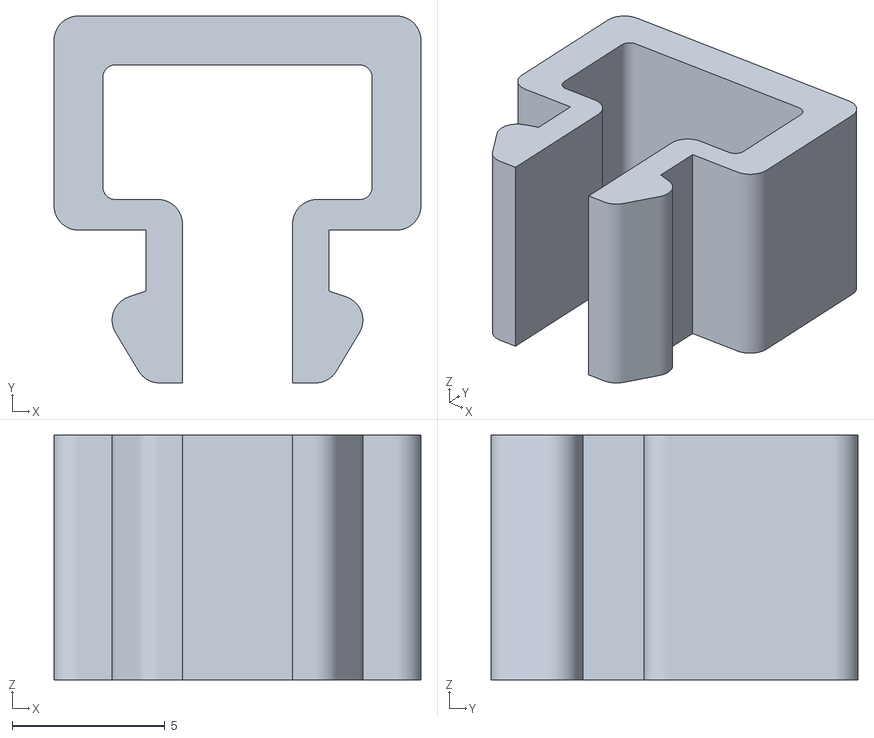
[picture p78: CAD file, 2023-08-16]
stl/Frame/clip_small.stl
12.0 x 12.0 x 8.00
