bowseruk/voron-2-300/stl/Panel Mount/bottom_panel_maghold_panel_x6.stl

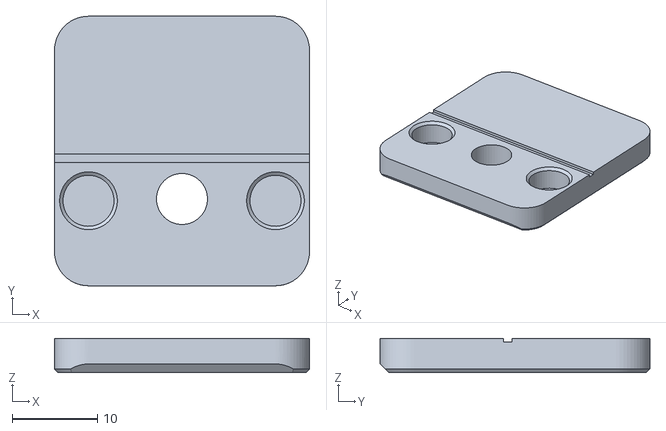
[picture p79: CAD file, 2023-08-30]
stl/Panel Mount/bottom_panel_maghold_panel_x6.stl
30.0 x 31.7 x 4.00
