bowseruk/voron-2-300/stl/Skirts/keystone_panel.stl

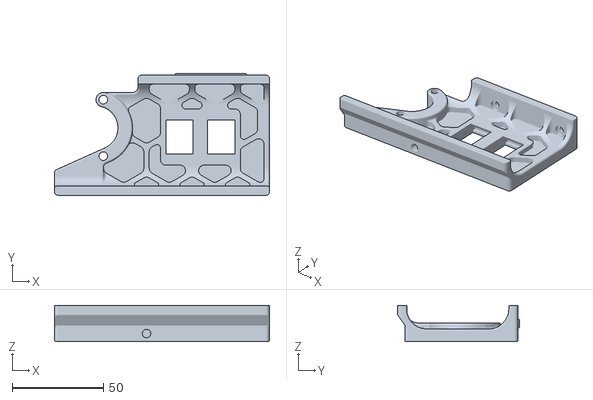
[picture p80: CAD file, 2023-08-16]
stl/Skirts/keystone_panel.stl
118.0 x 66.8 x 20.0
