bowseruk/voron-2-300/stl/Tools/bottom_panel_template.stl

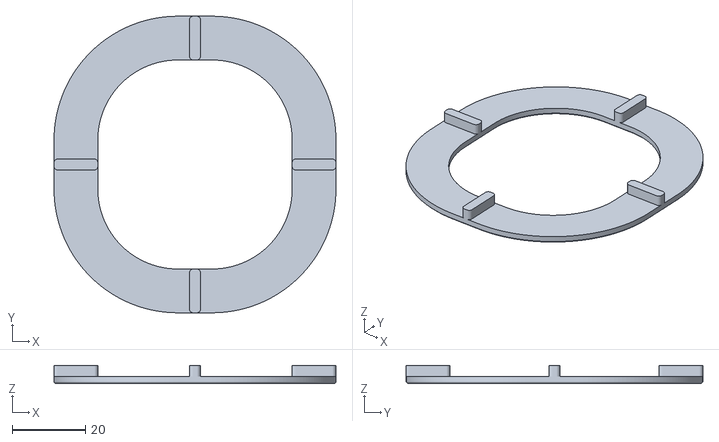
[picture p81: CAD file, 2023-08-16]
stl/Tools/bottom_panel_template.stl
77.2 x 81.2 x 5.00
