bowseruk/voron-2-300/stl/Electronics Bay/Octopus_bracket_set.stl

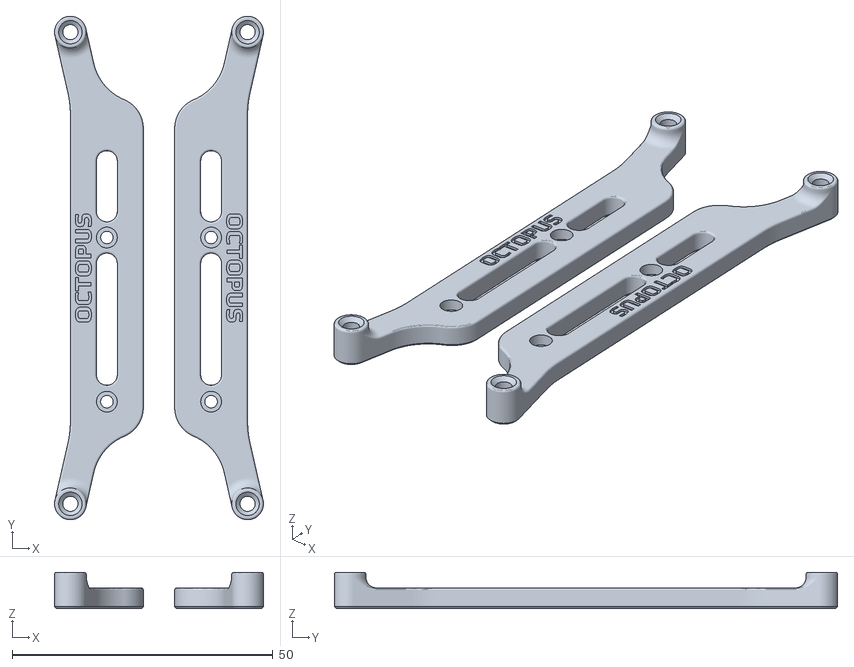
[picture p82: CAD file, 2023-08-16]
stl/Electronics Bay/Octopus_bracket_set.stl
40.1 x 96.6 x 7.00
