bowseruk/voron-2-300/stl/Frame/C920_Top_Front_Mount.stl

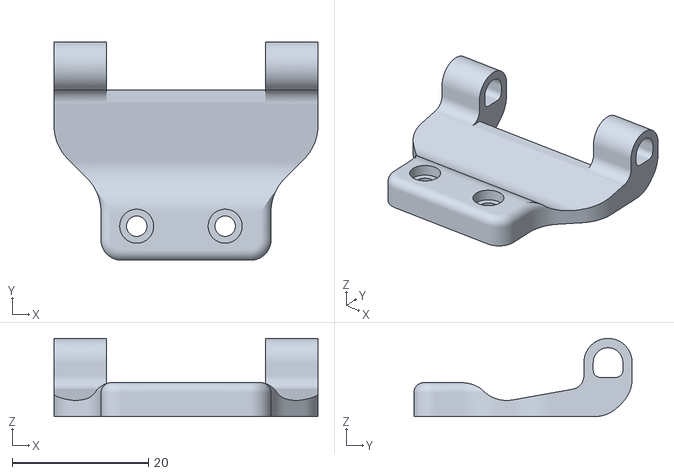
[picture p83: CAD file, 2023-08-16]
stl/Frame/C920_Top_Front_Mount.stl
38.8 x 32.1 x 11.5
