bowseruk/voron-2-300/stl/Gantry/z_chain_bottom_anchor.stl

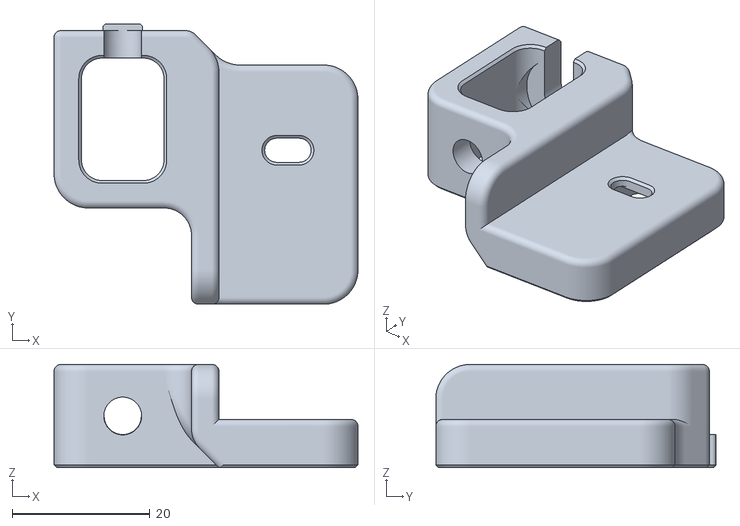
[picture p84: CAD file, 2023-08-16]
stl/Gantry/z_chain_bottom_anchor.stl
44.2 x 40.8 x 15.0
