bowseruk/voron-2-300/stl/Panel Mount/bottom_panel_magclip_skirt_x6.stl

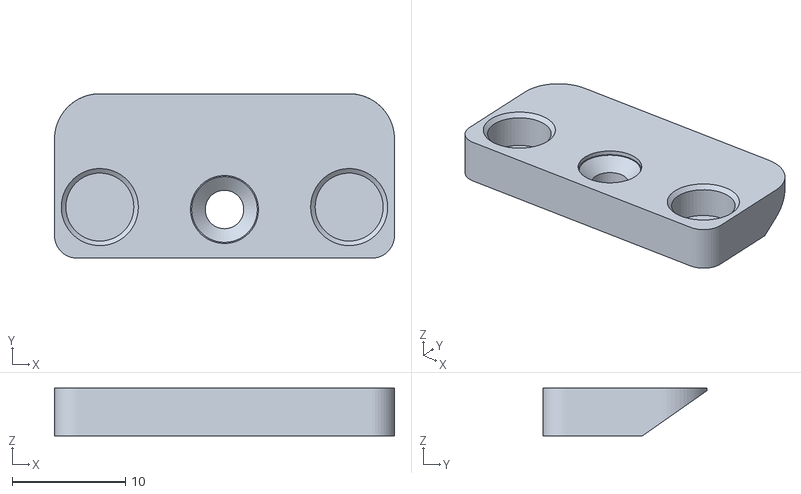
[picture p85: CAD file, 2023-08-30]
stl/Panel Mount/bottom_panel_magclip_skirt_x6.stl
30.0 x 14.5 x 4.20
