bowseruk/voron-2-300/stl/Skirts/side_skirt_b_300_x2.stl

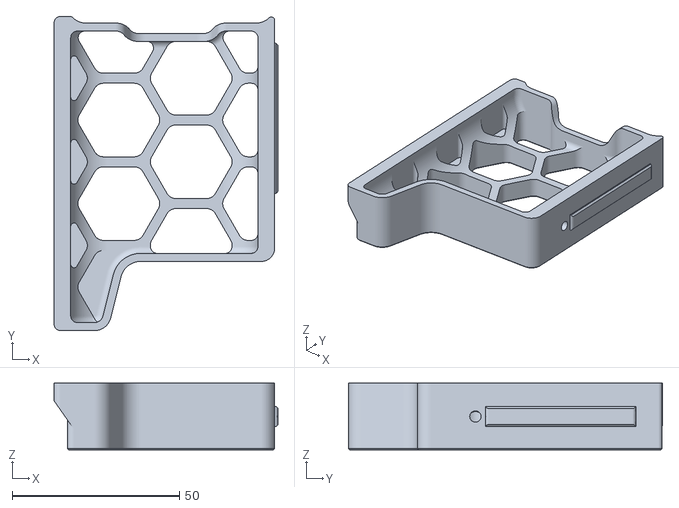
[picture p86: CAD file, 2023-08-16]
stl/Skirts/side_skirt_b_300_x2.stl
67.0 x 94.0 x 20.0
