bowseruk/voron-2-300/stl/Tools/[a]_latch.stl

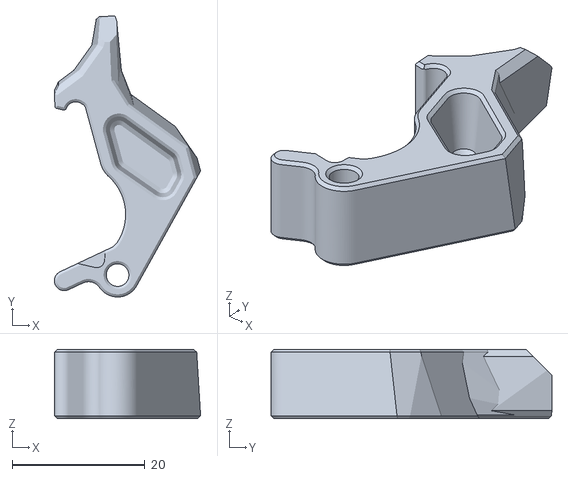
[picture p87: CAD file, 2023-08-16]
stl/Tools/[a]_latch.stl
22.0 x 42.3 x 10.4
