bowseruk/voron-2-300/stl/Electronics Bay/lrs_200_psu_bracket_x2.stl

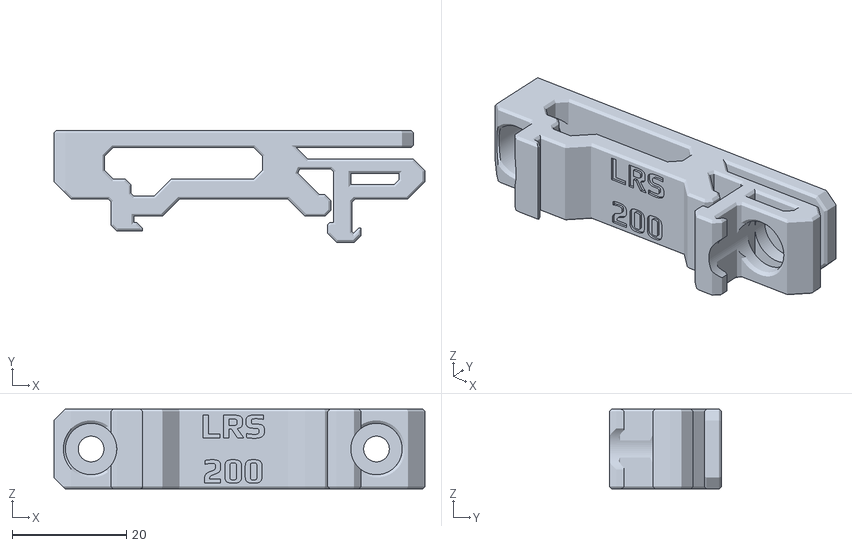
[picture p88: CAD file, 2023-08-16]
stl/Electronics Bay/lrs_200_psu_bracket_x2.stl
65.0 x 19.6 x 14.0
