bowseruk/voron-2-300/stl/Frame/[a]_extrusion_thermistor_mount.stl

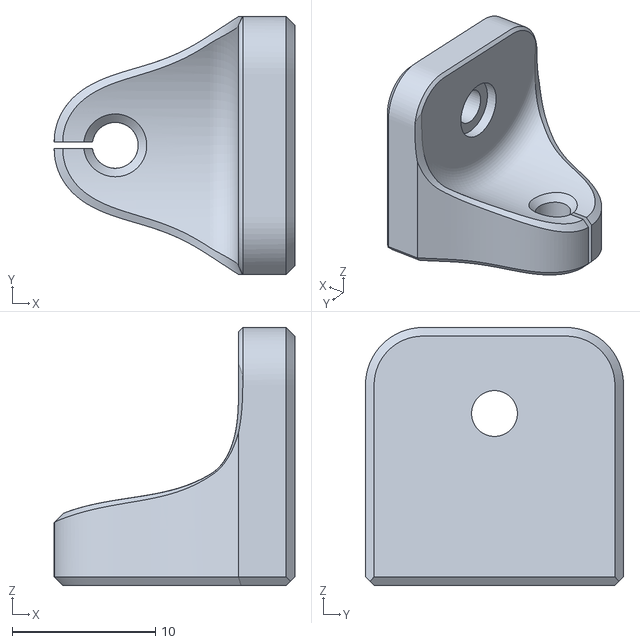
[picture p89: CAD file, 2023-08-16]
stl/Frame/[a]_extrusion_thermistor_mount.stl
16.8 x 18.0 x 18.0
