bowseruk/voron-2-300/stl/Gantry/[a]_z_belt_clip_lower_x4.stl

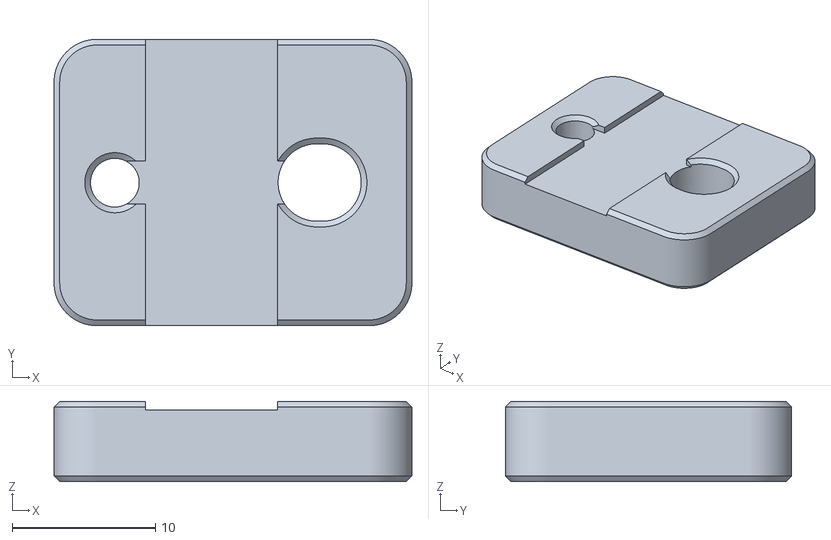
[picture p90: CAD file, 2023-08-16]
stl/Gantry/[a]_z_belt_clip_lower_x4.stl
25.0 x 20.0 x 5.60
