bowseruk/voron-2-300/stl/Panel Mount/Z Belt Pi Cam B Logo.stl

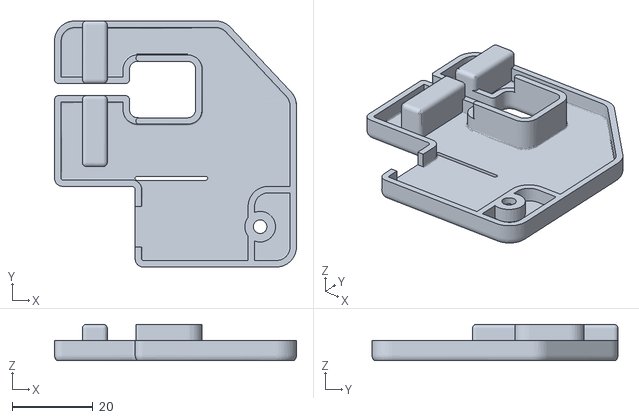
[picture p91: CAD file, 2023-08-30]
stl/Panel Mount/Z Belt Pi Cam B Logo.stl
60.0 x 61.0 x 9.00
