bowseruk/voron-2-300/stl/Frame/Brackets_2020.stl

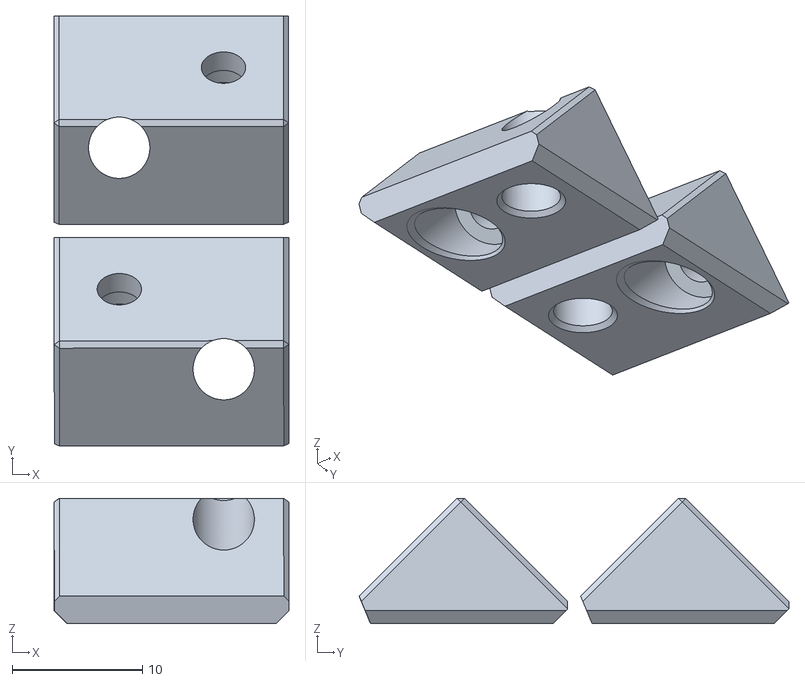
[picture p92: CAD file, 2023-08-16]
stl/Frame/Brackets_2020.stl
18.0 x 33.0 x 9.62
