bowseruk/voron-2-300/stl/Gantry/z_belt_clipX4.stl

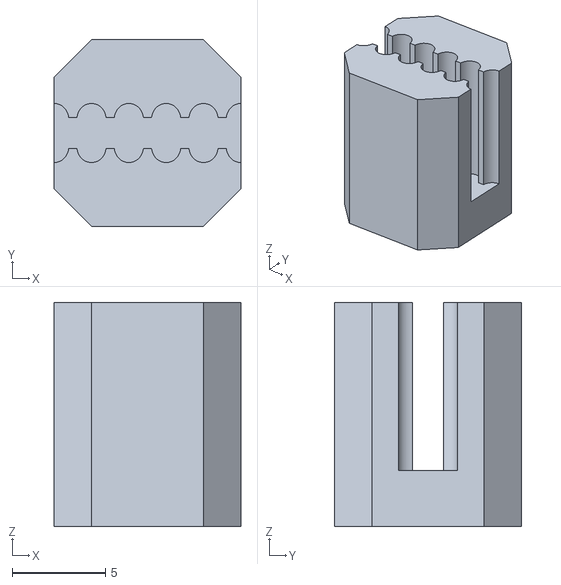
[picture p93: CAD file, 2023-08-16]
stl/Gantry/z_belt_clipX4.stl
10.0 x 10.0 x 12.0
