bowseruk/voron-2-300/stl/Panel Mount/z_belt_cover_a_x2.stl

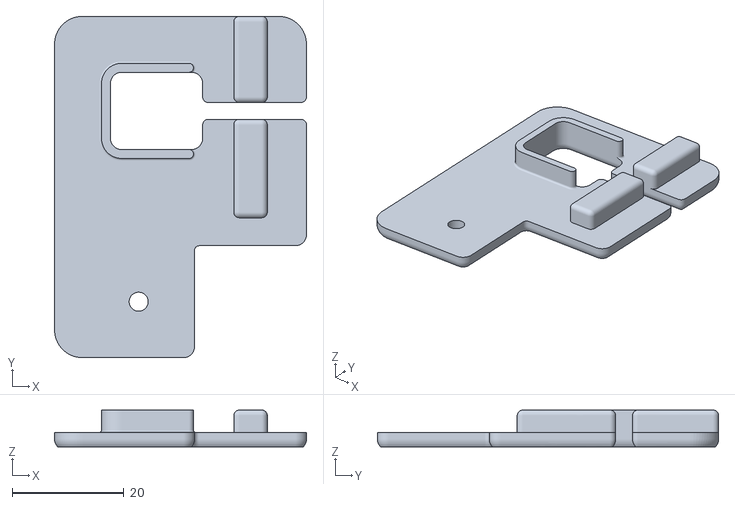
[picture p94: CAD file, 2023-08-16]
stl/Panel Mount/z_belt_cover_a_x2.stl
45.0 x 61.0 x 6.60
