bowseruk/voron-2-300/stl/Skirts/power_inlet_filtered.stl

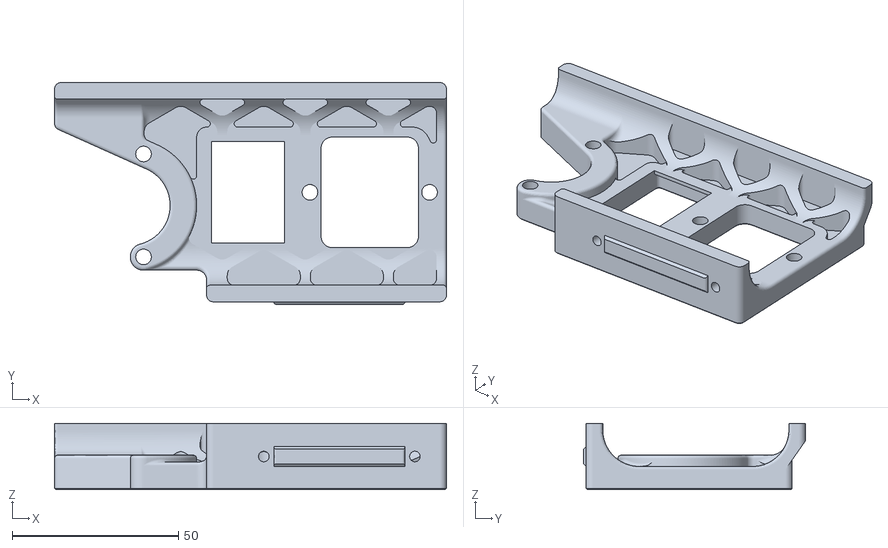
[picture p95: CAD file, 2023-08-16]
stl/Skirts/power_inlet_filtered.stl
118.0 x 66.8 x 20.0
