bowseruk/voron-2-300/stl/Tools/motor_plate.stl

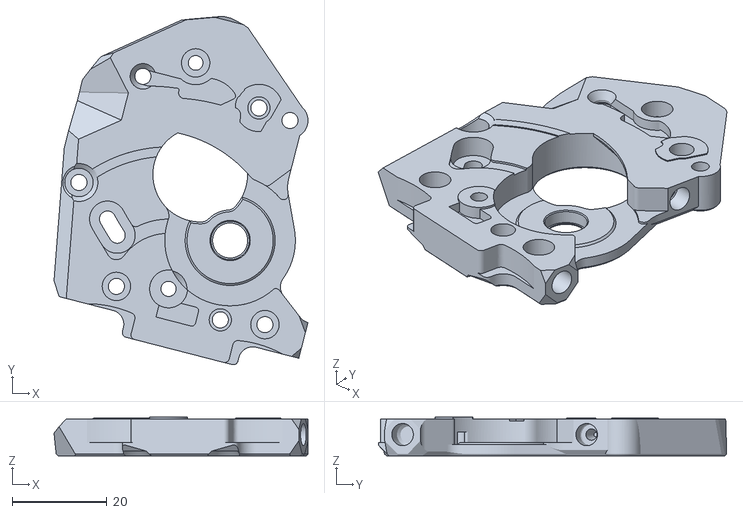
[picture p96: CAD file, 2023-08-16]
stl/Tools/motor_plate.stl
53.7 x 73.6 x 8.20
