bowseruk/voron-2-300/stl/Frame/BTT_Sensor_Mount_B.stl

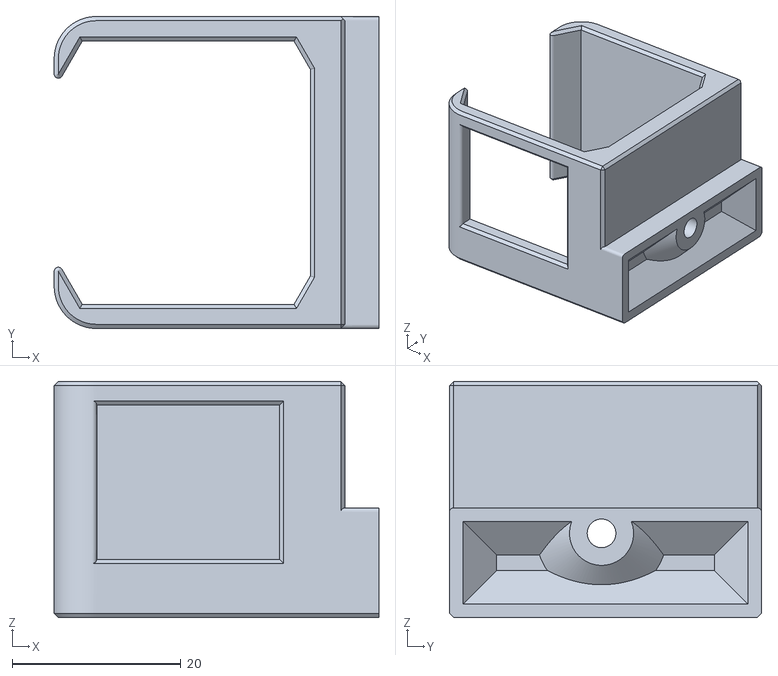
[picture p97: CAD file, 2023-08-16]
stl/Frame/BTT_Sensor_Mount_B.stl
38.5 x 37.0 x 28.0
