bowseruk/voron-2-300/stl/Panel Mount/midspan_panel_clip_6mm_x8.stl

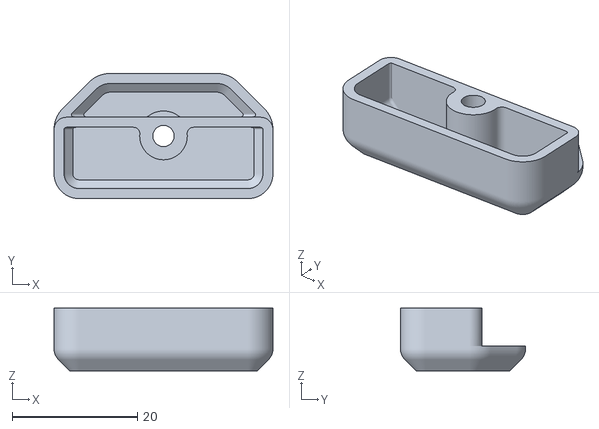
[picture p98: CAD file, 2023-08-16]
stl/Panel Mount/midspan_panel_clip_6mm_x8.stl
35.0 x 20.0 x 10.00
