bowseruk/voron-2-300/stl/Frame/BTT_Sensor_Mount_A.stl

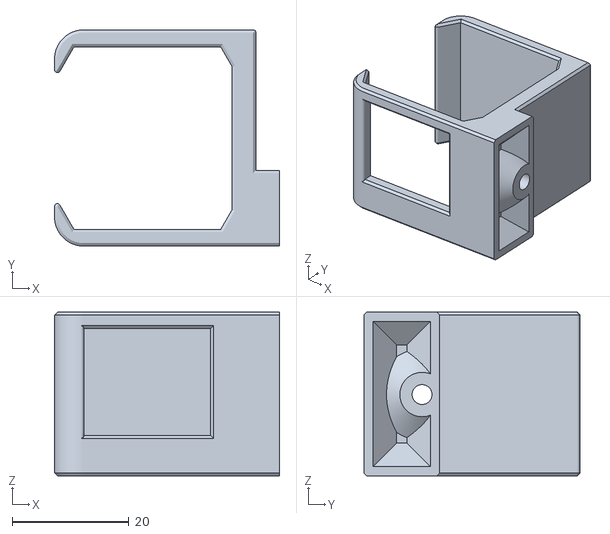
[picture p99: CAD file, 2023-08-16]
stl/Frame/BTT_Sensor_Mount_A.stl
38.5 x 37.0 x 28.0
