bowseruk/voron-2-300/stl/Frame/VoronZPiCamMount11.stl

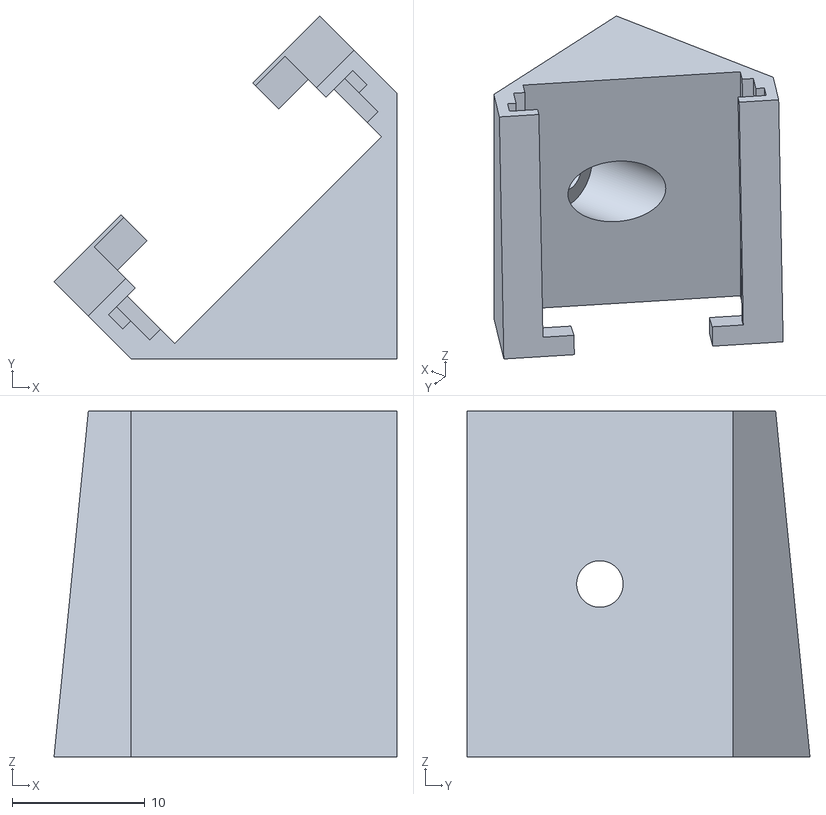
[picture p100: CAD file, 2023-08-16]
stl/Frame/VoronZPiCamMount11.stl
25.8 x 25.8 x 26.0
