bowseruk/voron-2-300/stl/Panel Mount/midspan_panel_clip_4mm_x7.stl

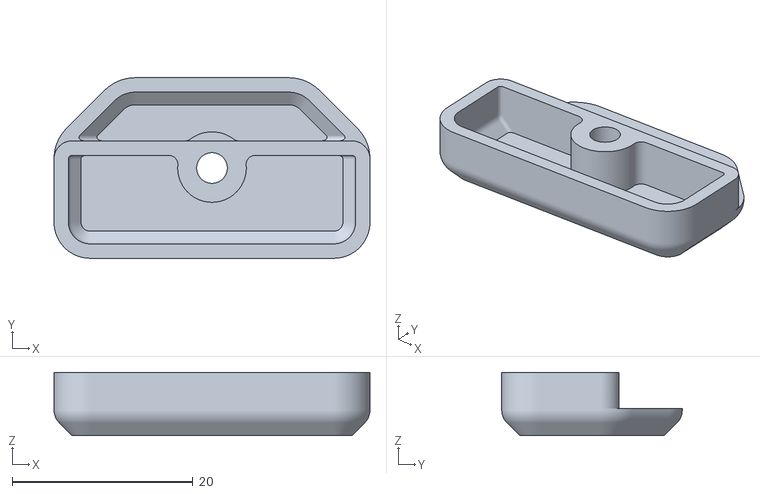
[picture p101: CAD file, 2023-08-16]
stl/Panel Mount/midspan_panel_clip_4mm_x7.stl
35.0 x 20.0 x 7.00
