bowseruk/voron-2-300/stl/Skirts/[a]_btt_knob_light_shield.stl

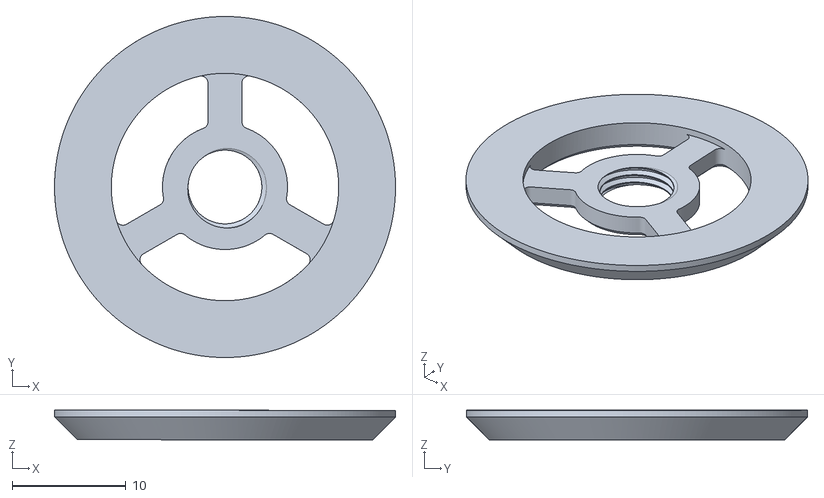
[picture p102: CAD file, 2023-08-16]
stl/Skirts/[a]_btt_knob_light_shield.stl
30.0 x 30.0 x 2.62
