bowseruk/voron-2-300/stl/Panel Mount/deck_support_4mm_x8.stl

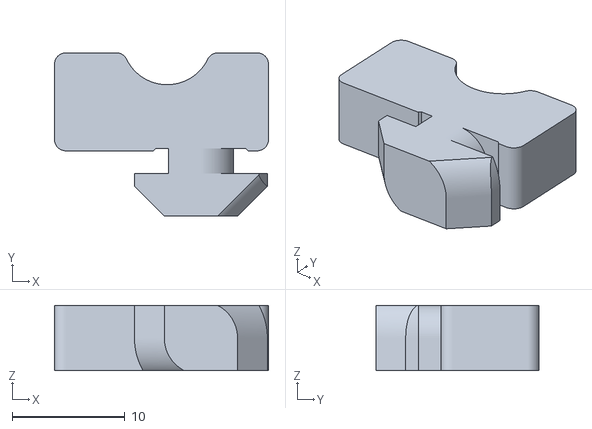
[picture p103: CAD file, 2023-08-16]
stl/Panel Mount/deck_support_4mm_x8.stl
19.0 x 14.5 x 5.80
