bowseruk/voron-2-300/stl/Skirts/ELFans_WagoMount.stl

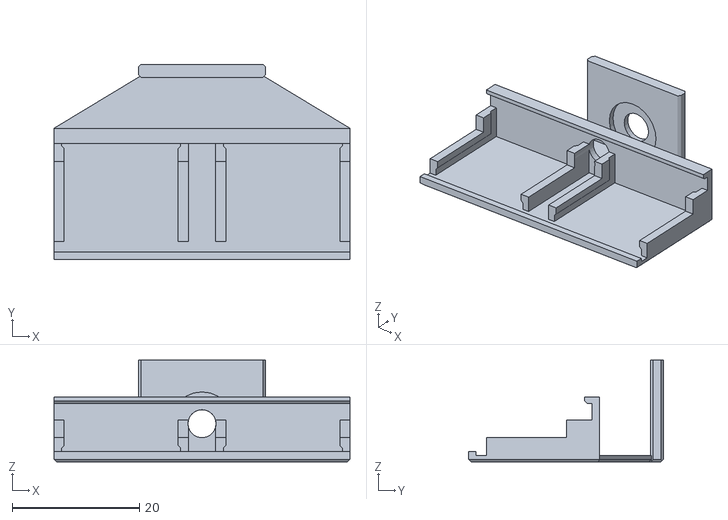
[picture p104: CAD file, 2023-08-16]
stl/Skirts/ELFans_WagoMount.stl
46.5 x 30.6 x 16.0
