bowseruk/voron-2-300/stl/Skirts/mini12864_case_front.stl

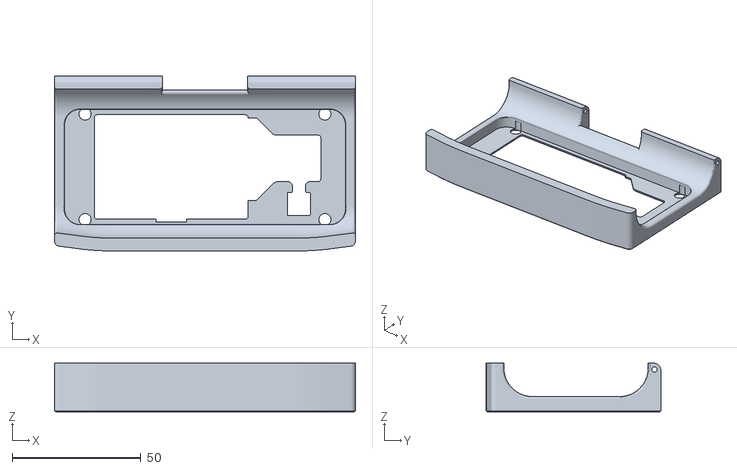
[picture p105: CAD file, 2023-08-16]
stl/Skirts/mini12864_case_front.stl
117.0 x 68.0 x 19.0
