bowseruk/voron-2-300/stl/Skirts/rear_center_skirt_300.stl

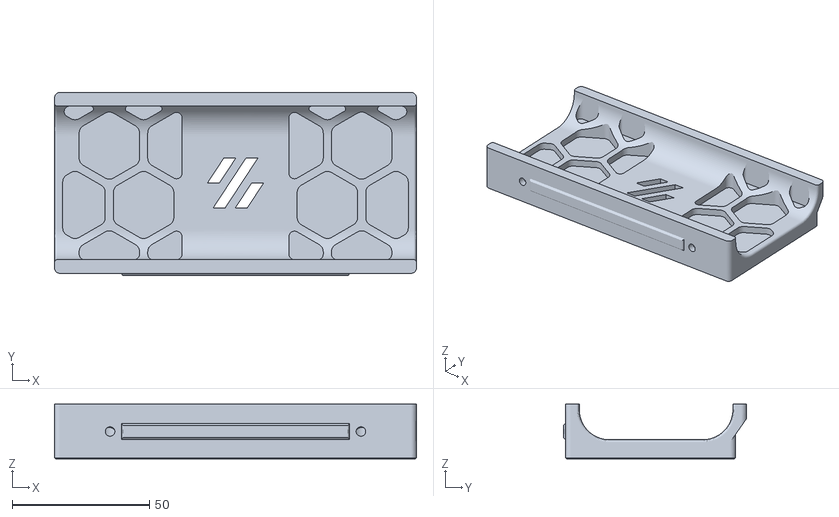
[picture p107: CAD file, 2023-08-16]
stl/Skirts/rear_center_skirt_300.stl
132.0 x 66.8 x 20.0
