bowseruk/voron-2-300/stl/Skirts/[a]_mini12864_case_front_insert.stl

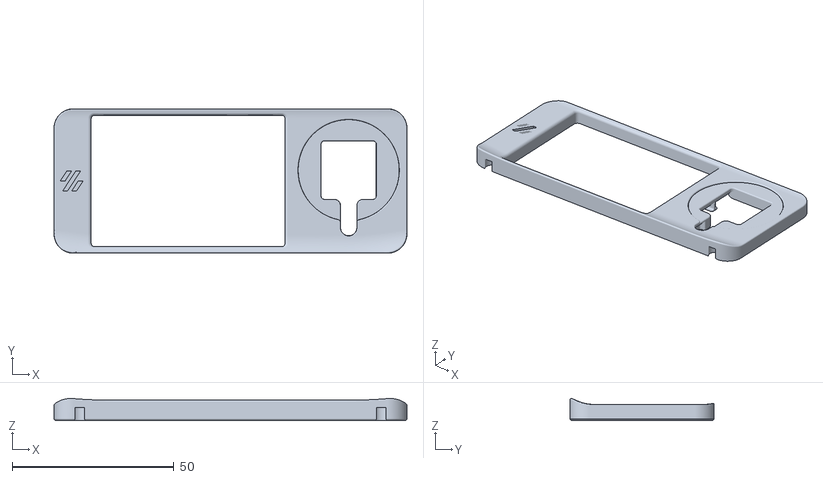
[picture p108: CAD file, 2023-08-16]
stl/Skirts/[a]_mini12864_case_front_insert.stl
109.0 x 44.6 x 6.81
