bowseruk/voron-2-300/config/printer_data/klipper/pitb.cfg

#####################################################################
#   Introduction
#####################################################################

# This file has the connection to the Fysetc PITB board.
# It also stores the alias information for it.

#####################################################################
#   MCU Information
#####################################################################

[mcu PITB]
canbus_uuid: 261931fc8408

#####################################################################
#   Fysetc PITB Aliases
#####################################################################

[board_pins PITB]
mcu: PITB
aliases:
    ## Board enable LED
    LED_RUN=gpio15,

    ## Can pins. STANDBY can be pulled low if you're running USB to disable the transceiver
    ## https://www.nxp.com/docs/en/data-sheet/TJA1040.pdf page 4
    CAN_TX=gpio13, CAN_RX=gpio14, CAN_STANDBY=gpio25,

    ## SPI for motors. spi_bus: spi0a
    MISO=gpio0, MOSI=gpio3, SCLK=gpio2,

    ## Stepper pins
    MOT1_EN=gpio5, MOT1_CS=gpio6,  MOT1_DIR=gpio7,  MOT1_STEP=gpio8,
    MOT2_EN=gpio9, MOT2_CS=gpio10, MOT2_DIR=gpio11, MOT2_STEP=gpio12,

    ## Endstop pins, or DIAG with jumpers
    ENDSTOP_X=gpio23, ENDSTOP_Y=gpio24,

    ## I2C bus: i2c0e
    SCL=gpio17, SDA=gpio16,

    ## Other IO
    FAN0=gpio20, FAN1=gpio21, THERM0=gpio26,
    RGB=gpio29,
